digilogistist/The-Open-Source-USB-NES-Project/cap_add/IMG_20220502_140206 - Copy.jpg

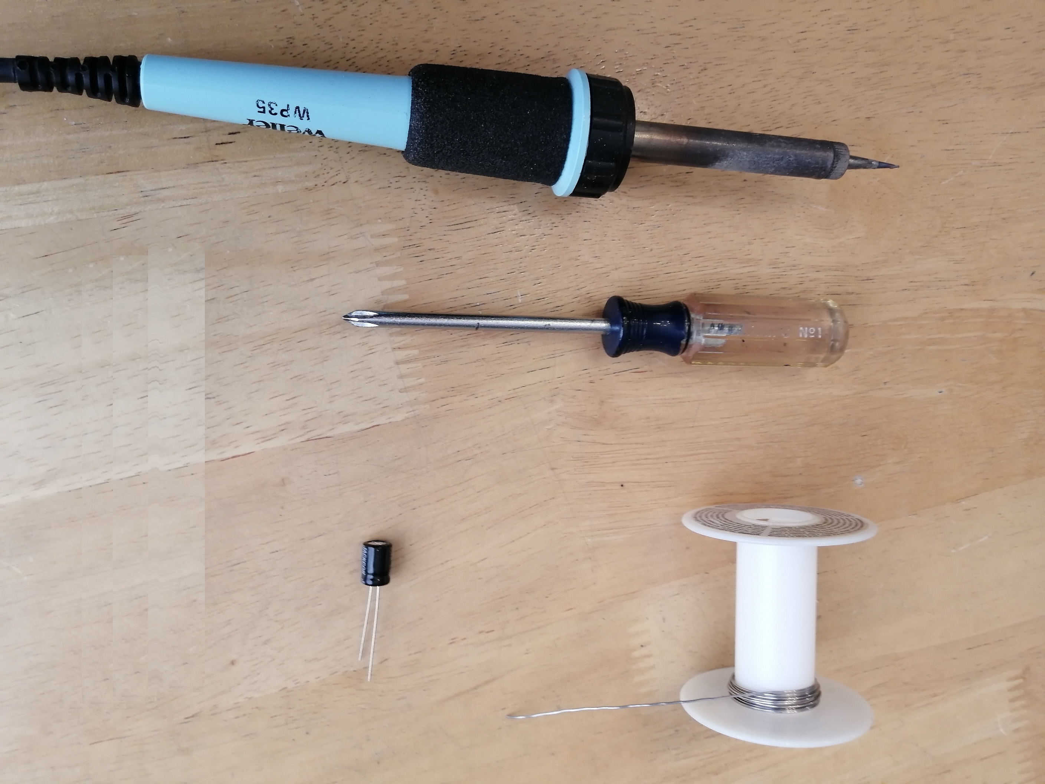
cap_add/IMG_20220502_140206 - Copy.jpg
