digilogistist/The-Open-Source-USB-NES-Project/cap_add/IMG_20220502_161517.jpg

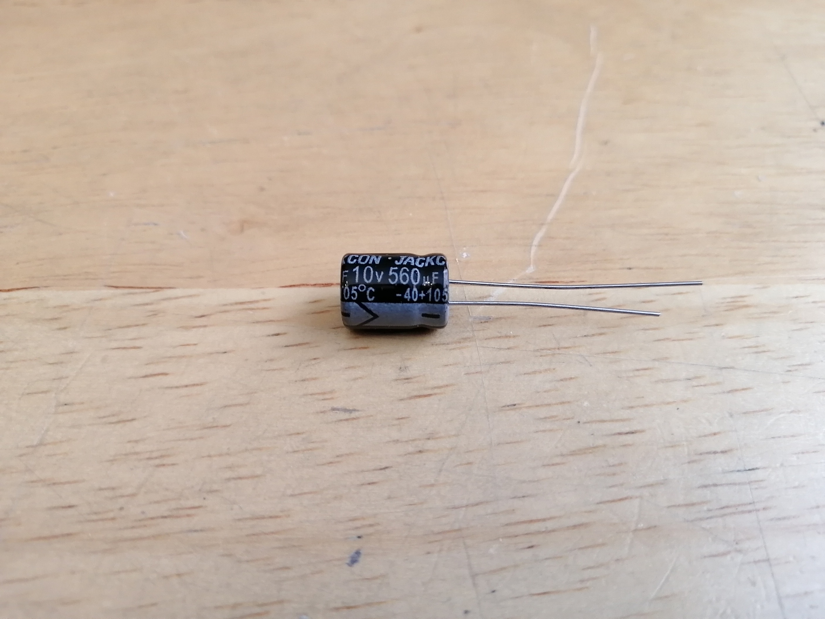
cap_add/IMG_20220502_161517.jpg
