digilogistist/The-Open-Source-USB-NES-Project/cap_add/IMG_20220503_070332.jpg

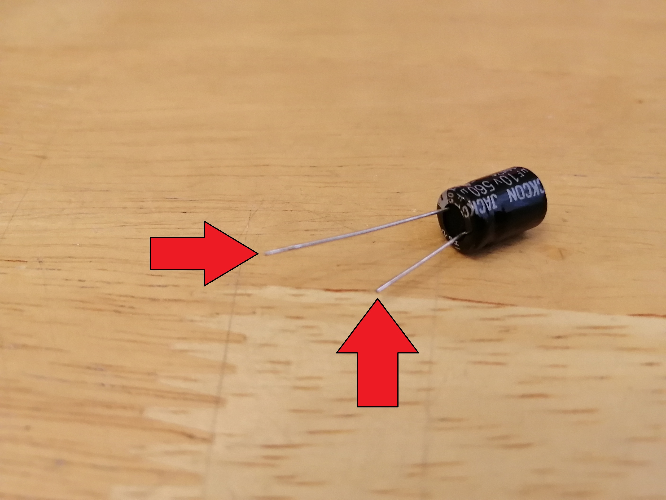
cap_add/IMG_20220503_070332.jpg
