digilogistist/The-Open-Source-USB-NES-Project/cap_add/IMG_20220503_071132.jpg

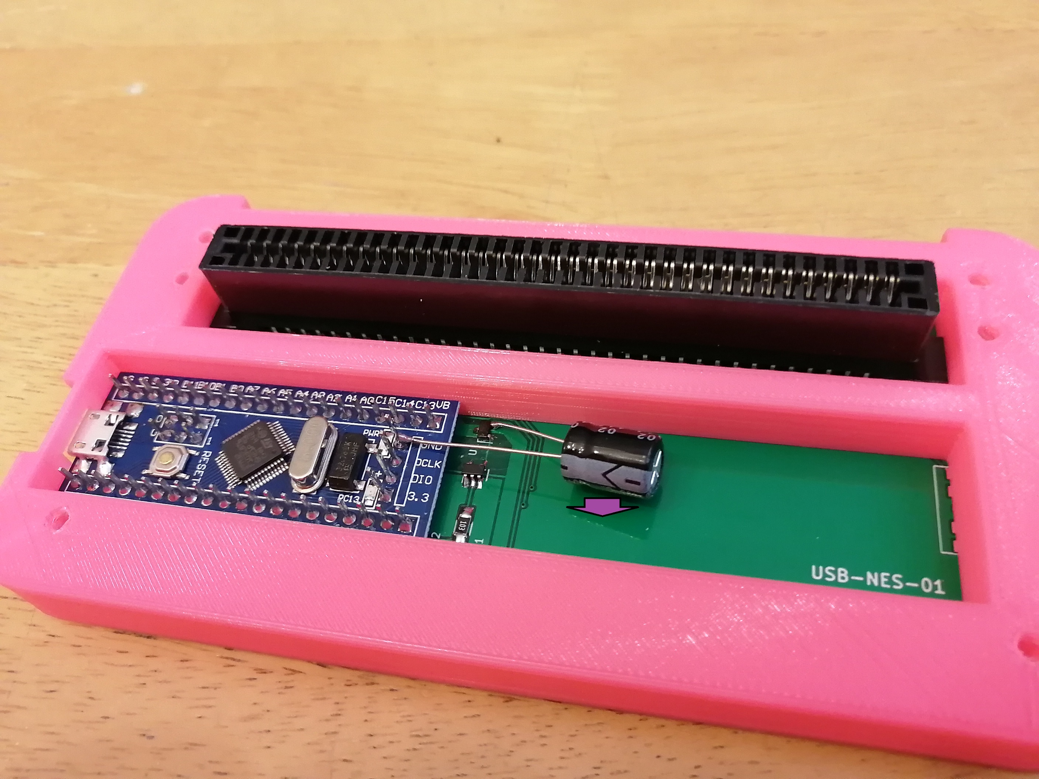
cap_add/IMG_20220503_071132.jpg
