digilogistist/The-Open-Source-USB-NES-Project/gallery/baby blue/IMG_20220524_081236.jpg

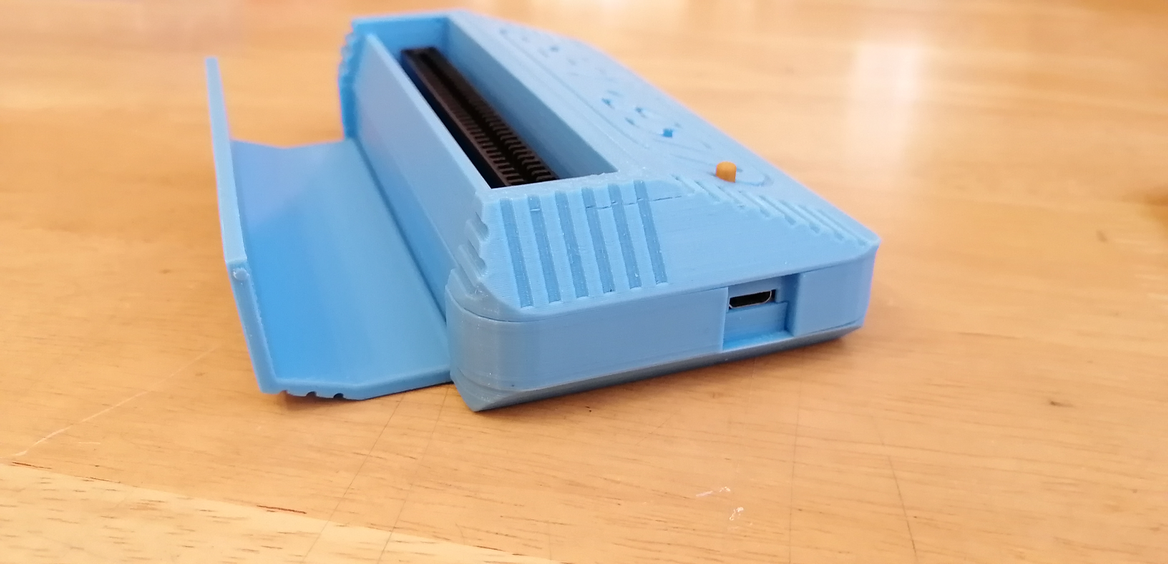
gallery/baby blue/IMG_20220524_081236.jpg
