digilogistist/The-Open-Source-USB-NES-Project/gallery/baby blue/IMG_20220524_081411.jpg

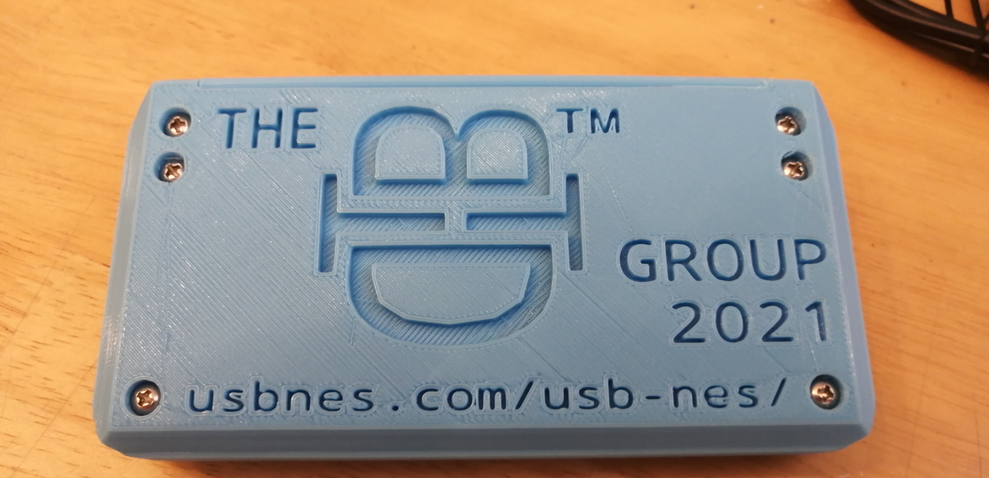
gallery/baby blue/IMG_20220524_081411.jpg
