digilogistist/The-Open-Source-USB-NES-Project/gallery/cartfail1.JPG

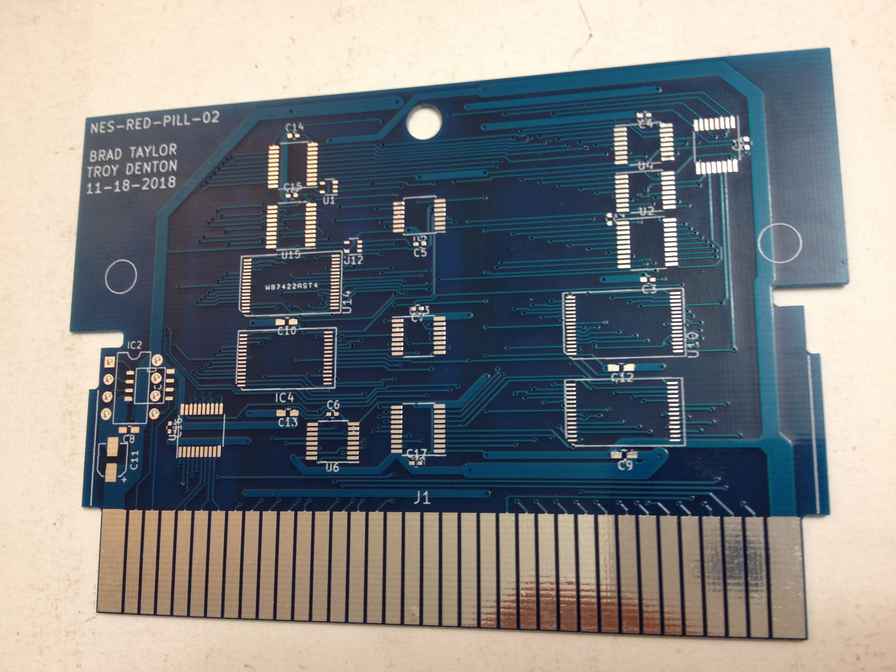
gallery/cartfail1.JPG
