digilogistist/The-Open-Source-USB-NES-Project/gallery/cartfail2.JPG

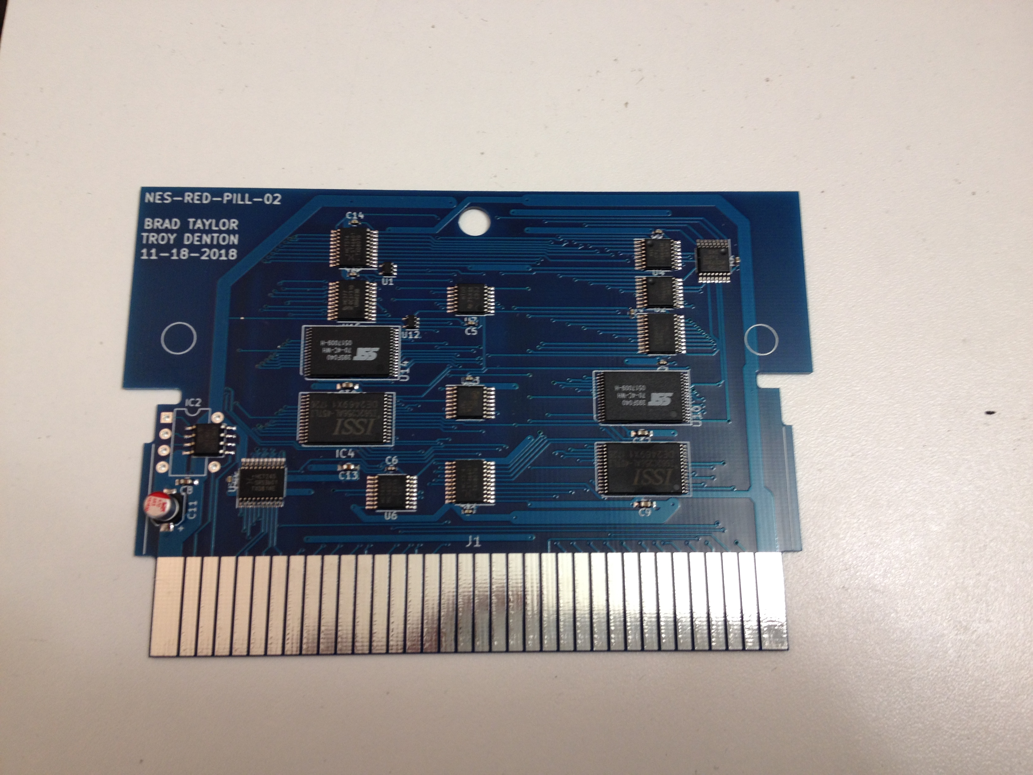
gallery/cartfail2.JPG
