digilogistist/The-Open-Source-USB-NES-Project/gallery/cartfail3.JPG

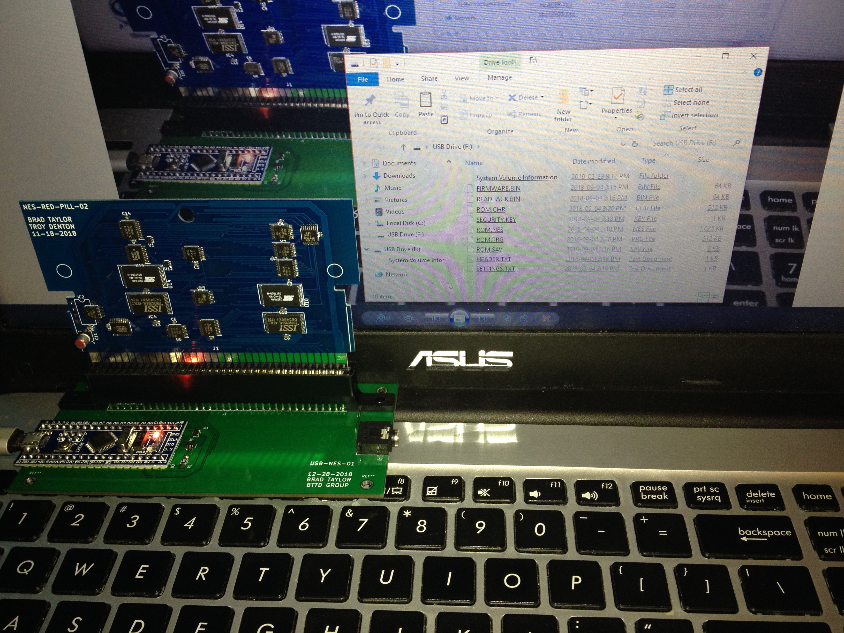
gallery/cartfail3.JPG
