digilogistist/The-Open-Source-USB-NES-Project/gallery/celluloid-shot0002.jpg

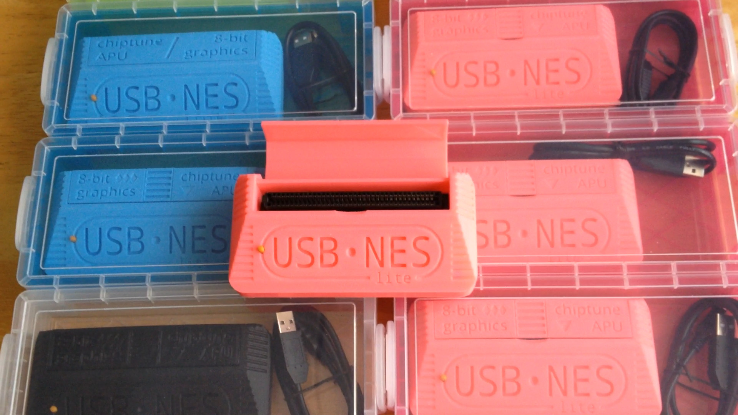
gallery/celluloid-shot0002.jpg
