digilogistist/The-Open-Source-USB-NES-Project/gallery/DIY kit/IMG_1746.JPG

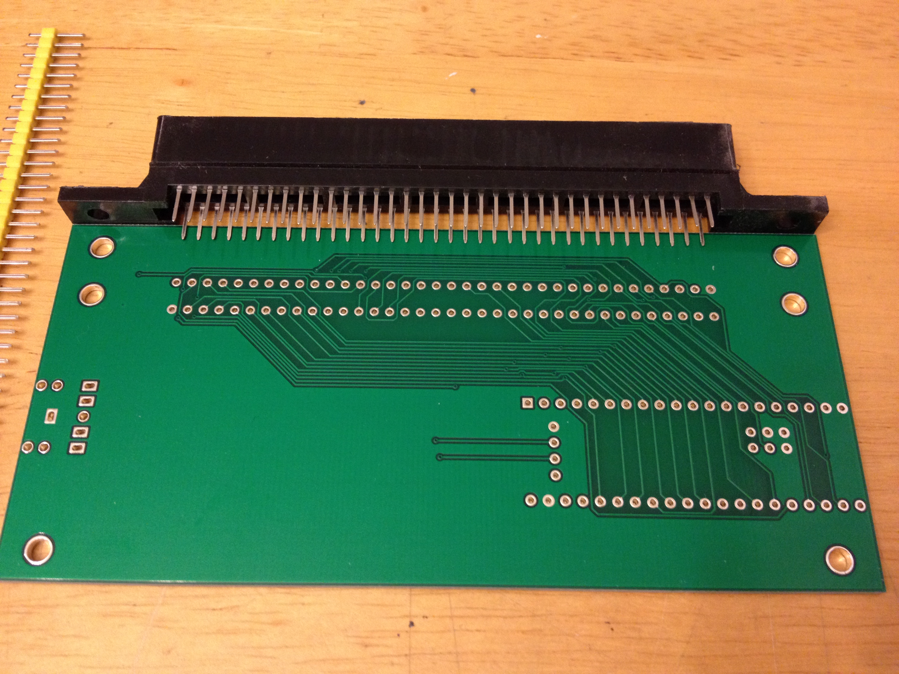
gallery/DIY kit/IMG_1746.JPG
