digilogistist/The-Open-Source-USB-NES-Project/gallery/DIY kit/IMG_1748.JPG

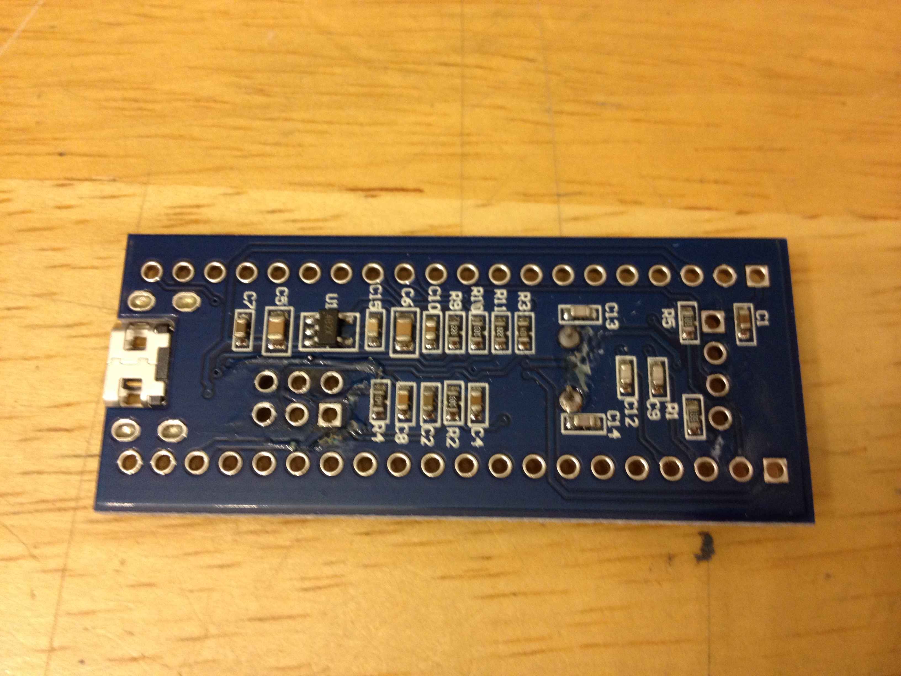
gallery/DIY kit/IMG_1748.JPG
