digilogistist/The-Open-Source-USB-NES-Project/gallery/DIY kit/IMG_1896.JPG

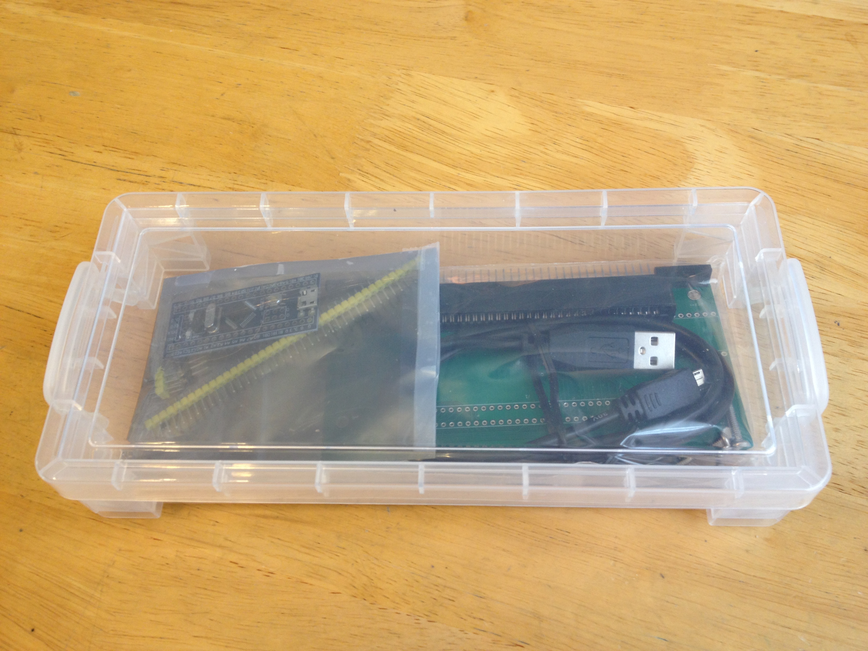
gallery/DIY kit/IMG_1896.JPG
