digilogistist/The-Open-Source-USB-NES-Project/gallery/DIY kit/IMG_1899.JPG

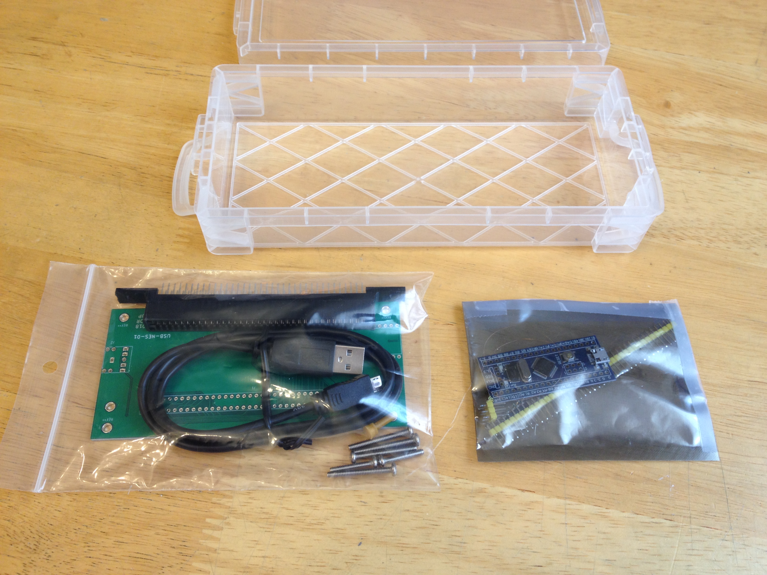
gallery/DIY kit/IMG_1899.JPG
