digilogistist/The-Open-Source-USB-NES-Project/gallery/fluorescent yellow/IMG_1937.JPG

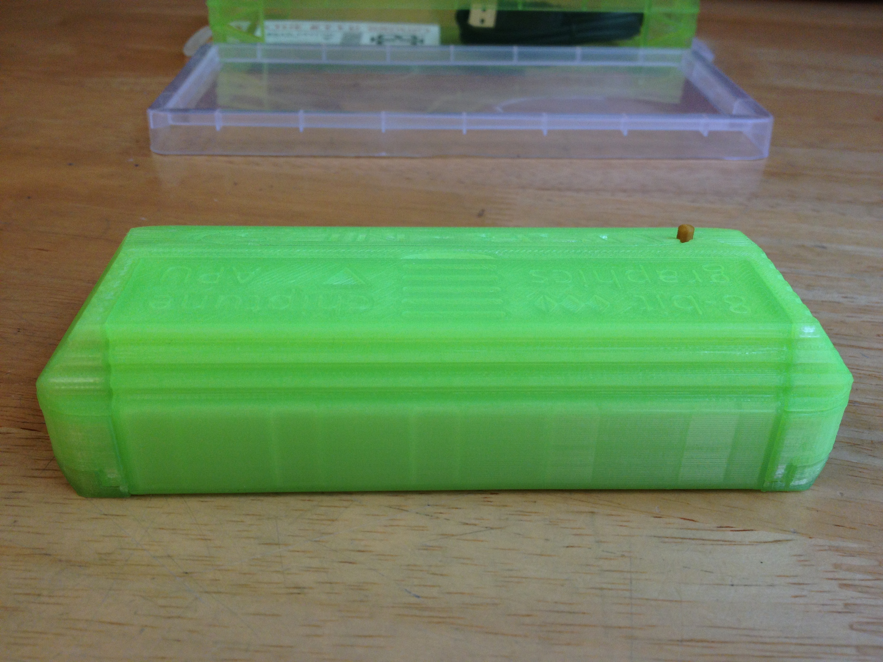
gallery/fluorescent yellow/IMG_1937.JPG
