digilogistist/The-Open-Source-USB-NES-Project/gallery/fluorescent yellow/IMG_1939.JPG

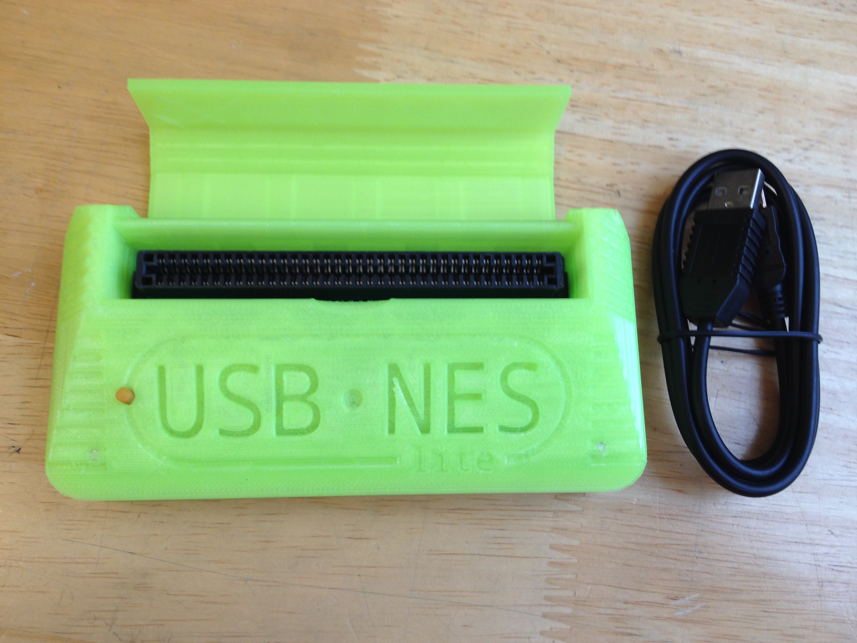
gallery/fluorescent yellow/IMG_1939.JPG
