digilogistist/The-Open-Source-USB-NES-Project/gallery/fluorescent yellow/IMG_1953.JPG

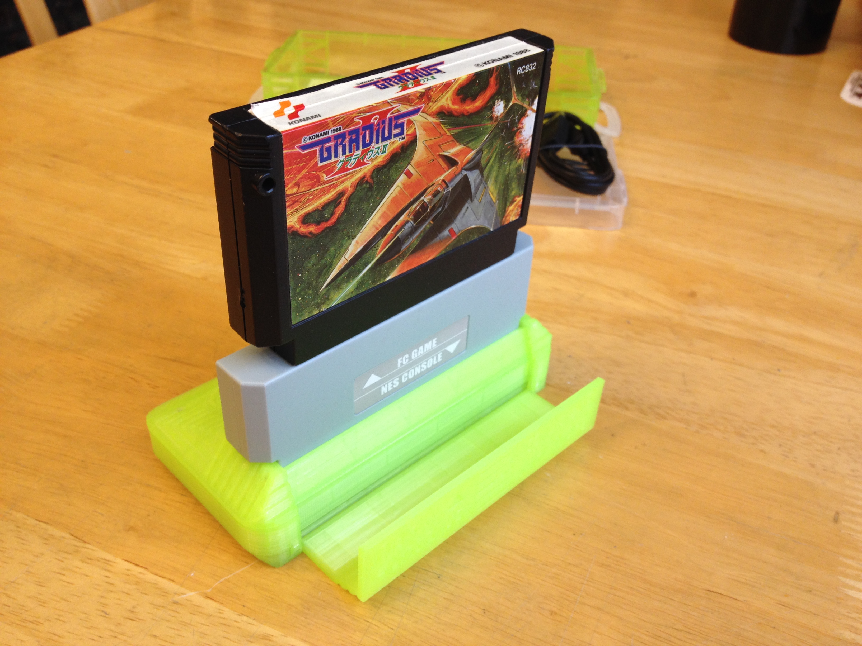
gallery/fluorescent yellow/IMG_1953.JPG
