digilogistist/The-Open-Source-USB-NES-Project/gallery/glittery gold/IMG_20230323_132124.jpg

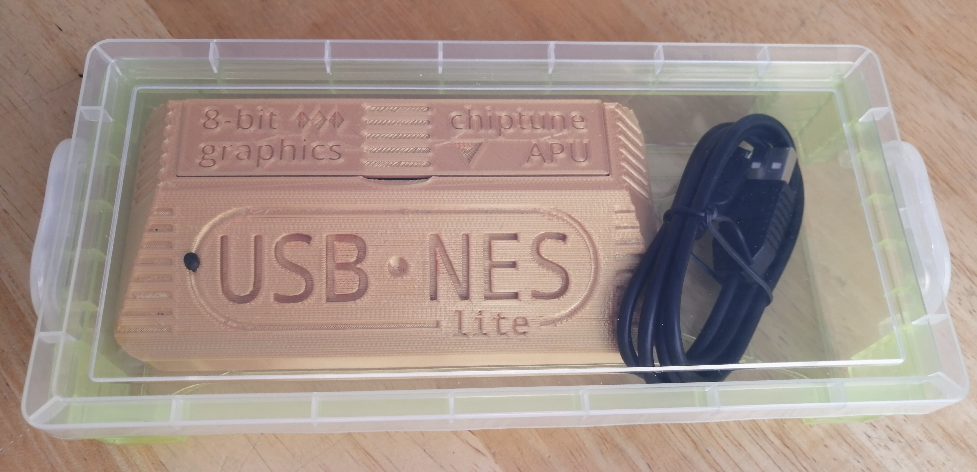
gallery/glittery gold/IMG_20230323_132124.jpg
