digilogistist/The-Open-Source-USB-NES-Project/gallery/glittery gold/IMG_20230323_132413.jpg

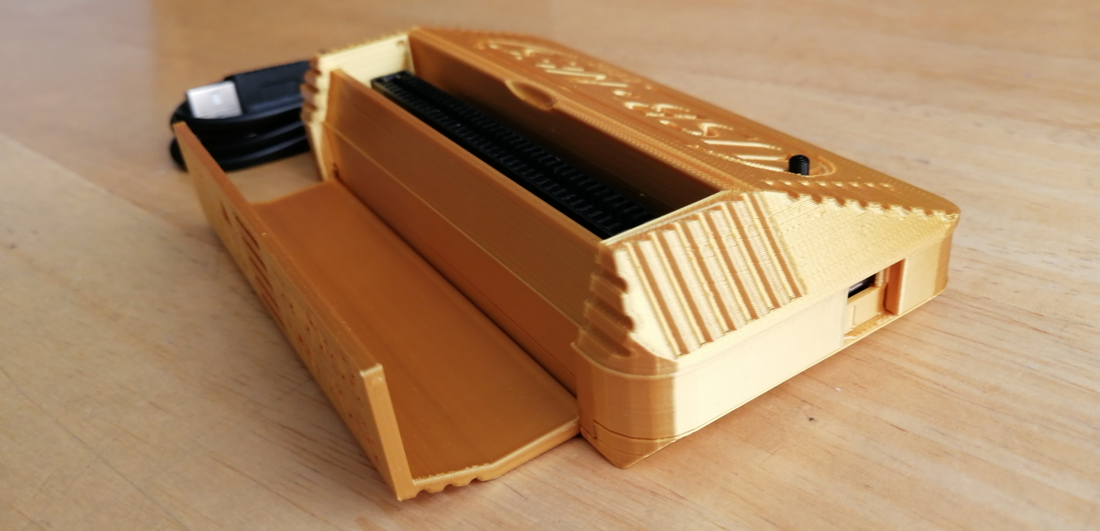
gallery/glittery gold/IMG_20230323_132413.jpg
