digilogistist/The-Open-Source-USB-NES-Project/gallery/gummy green/IMG_1789.JPG

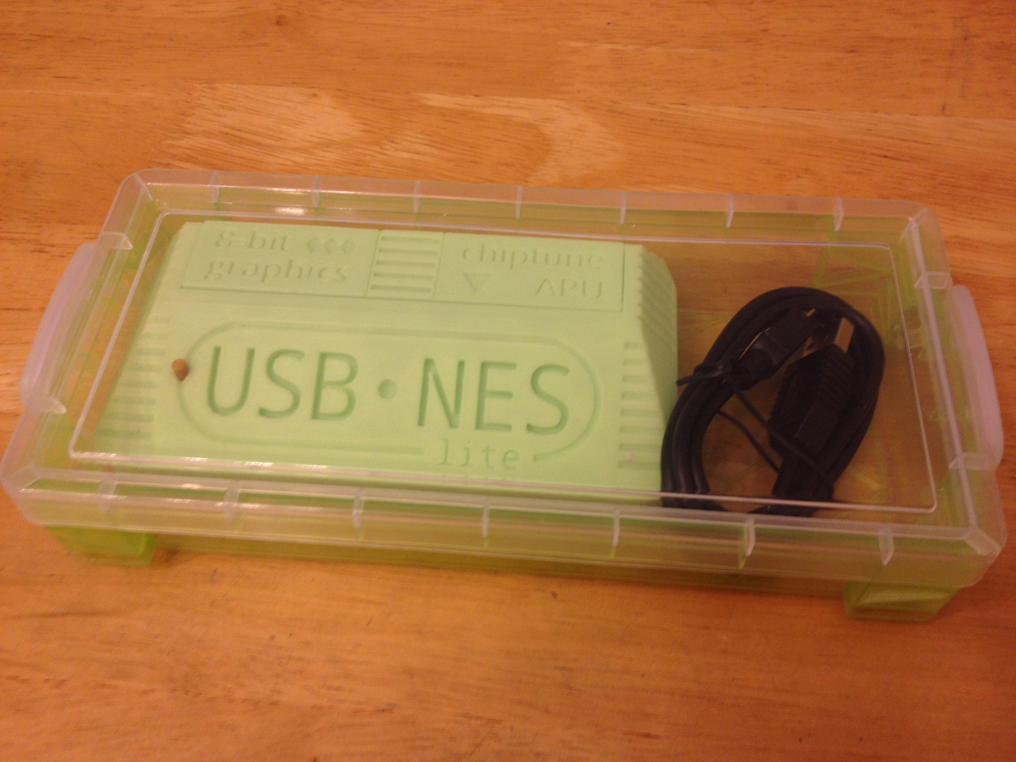
gallery/gummy green/IMG_1789.JPG
