digilogistist/The-Open-Source-USB-NES-Project/gallery/gummy green/IMG_1792.JPG

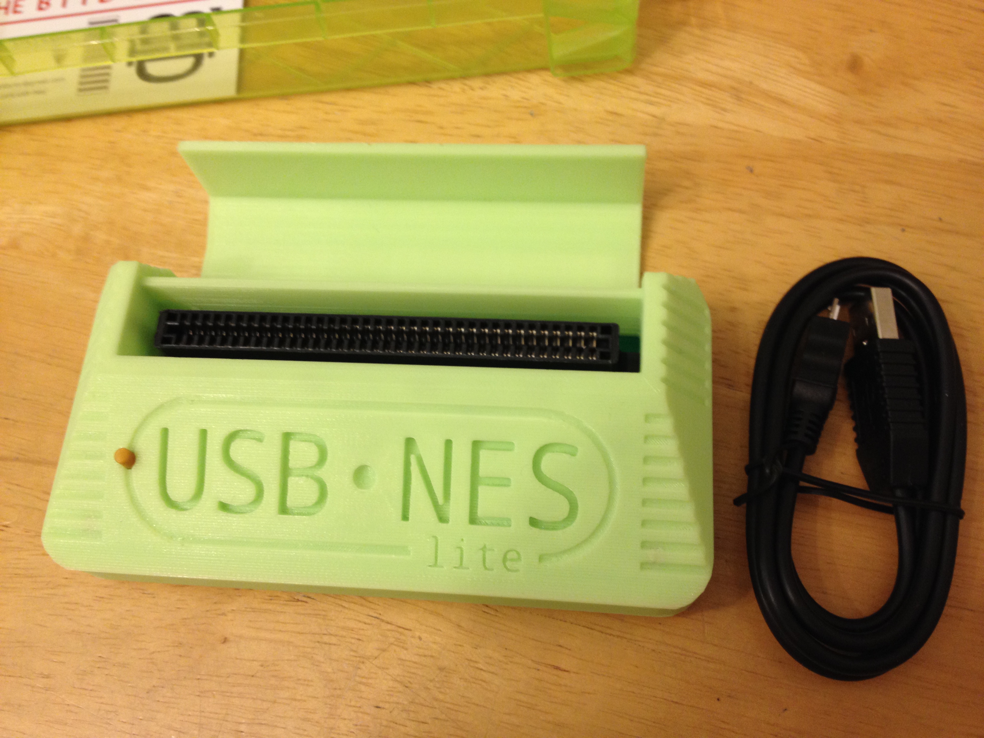
gallery/gummy green/IMG_1792.JPG
