digilogistist/The-Open-Source-USB-NES-Project/gallery/gummy green/IMG_1841.JPG

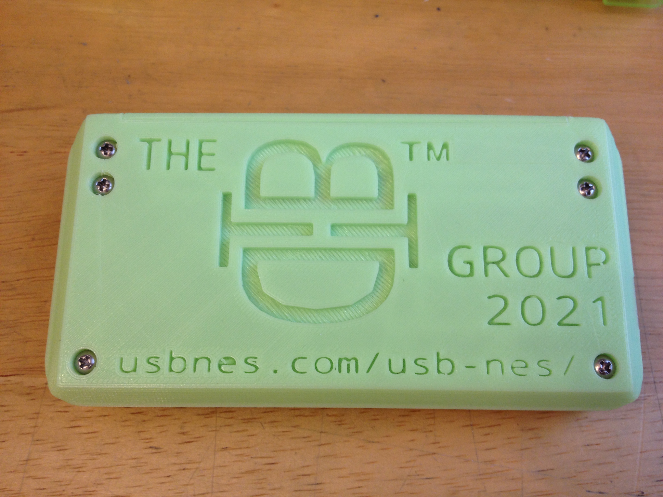
gallery/gummy green/IMG_1841.JPG
