digilogistist/The-Open-Source-USB-NES-Project/gallery/gummy green/IMG_1852.JPG

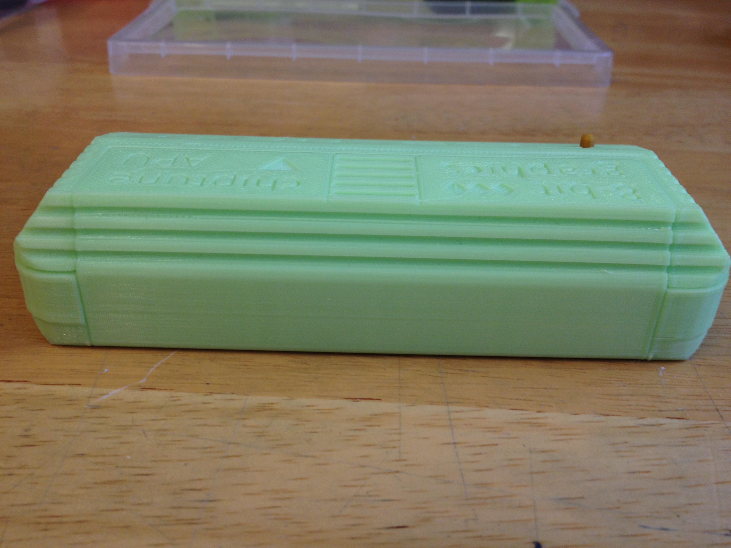
gallery/gummy green/IMG_1852.JPG
