digilogistist/The-Open-Source-USB-NES-Project/gallery/IMG_1150.JPG

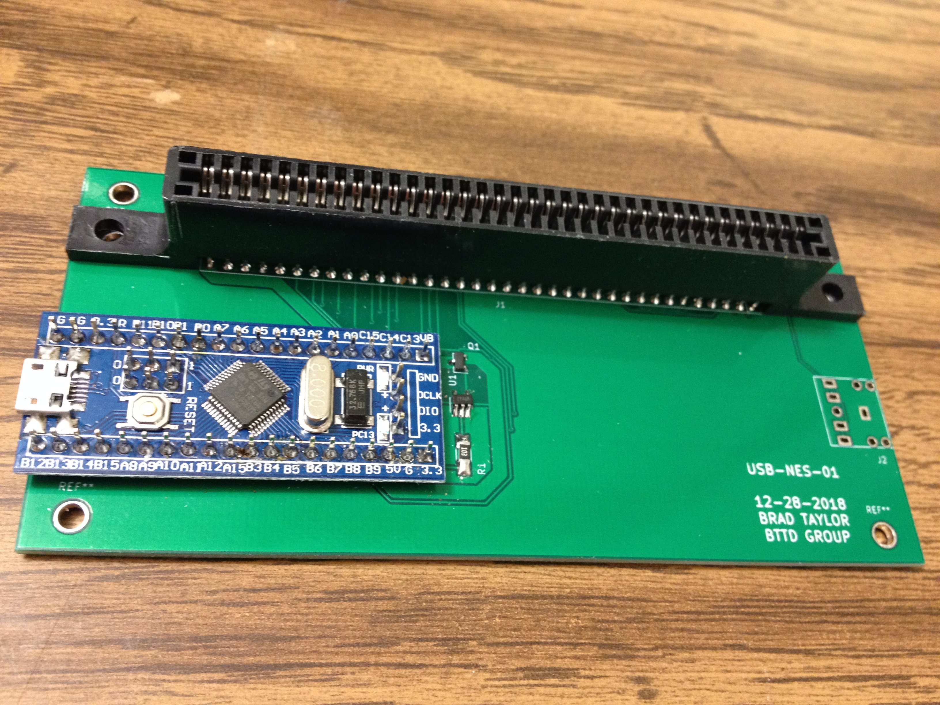
gallery/IMG_1150.JPG
