digilogistist/The-Open-Source-USB-NES-Project/gallery/IMG_1157.JPG

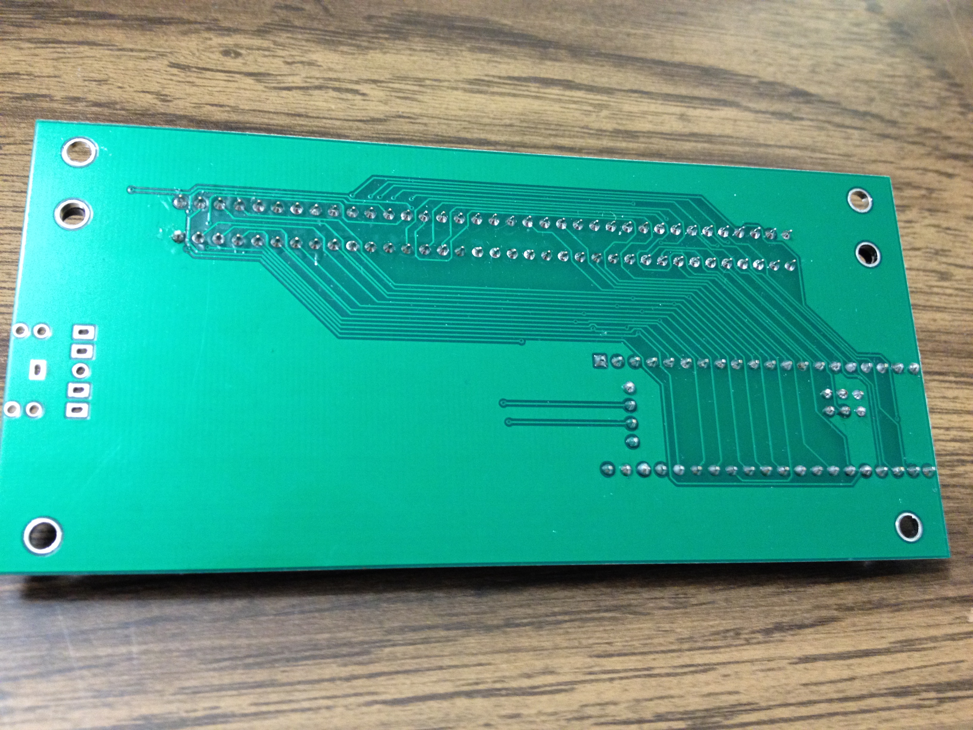
gallery/IMG_1157.JPG
