digilogistist/The-Open-Source-USB-NES-Project/gallery/IMG_1705.JPG

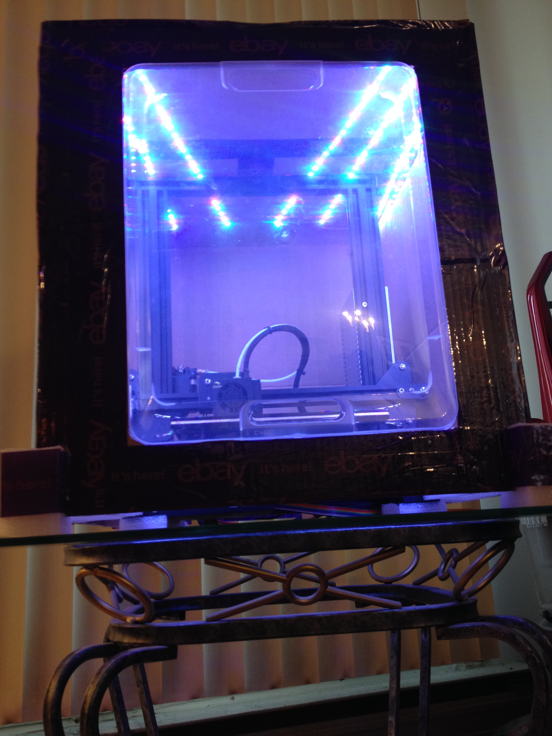
gallery/IMG_1705.JPG
