digilogistist/The-Open-Source-USB-NES-Project/gallery/IMG_1709.JPG

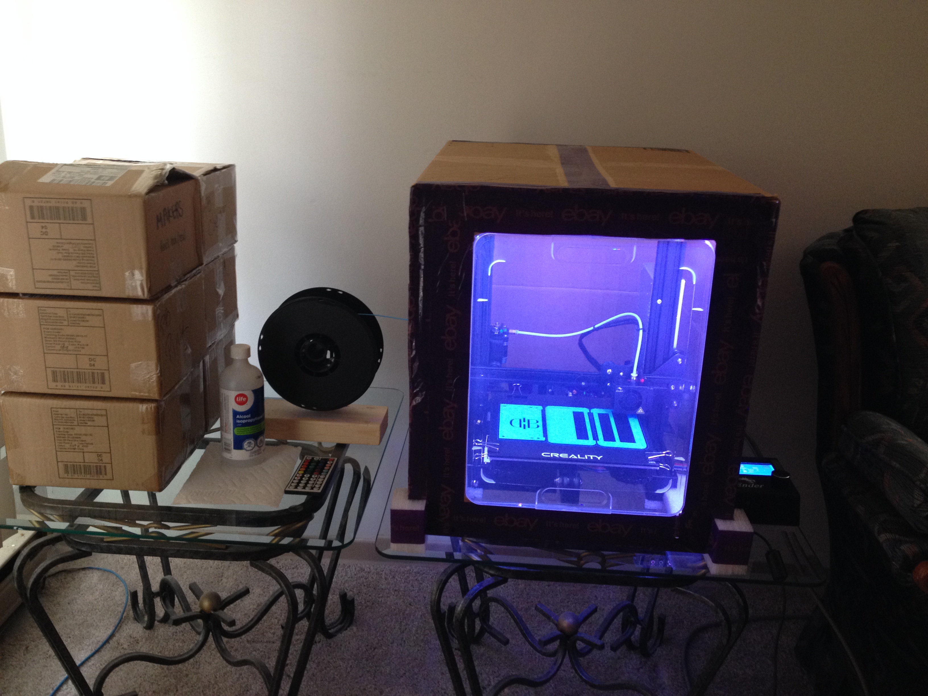
gallery/IMG_1709.JPG
