digilogistist/The-Open-Source-USB-NES-Project/gallery/IMG_1710.JPG

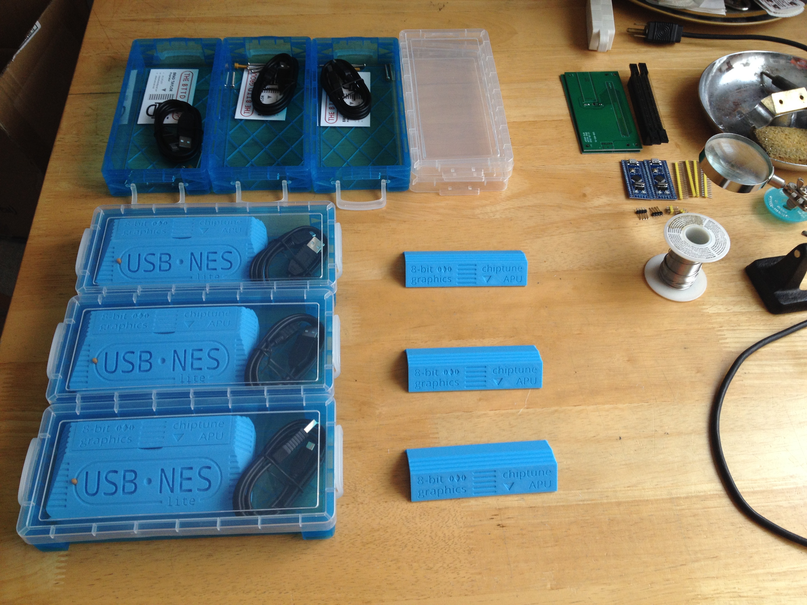
gallery/IMG_1710.JPG
