digilogistist/The-Open-Source-USB-NES-Project/gallery/IMG_1750.JPG

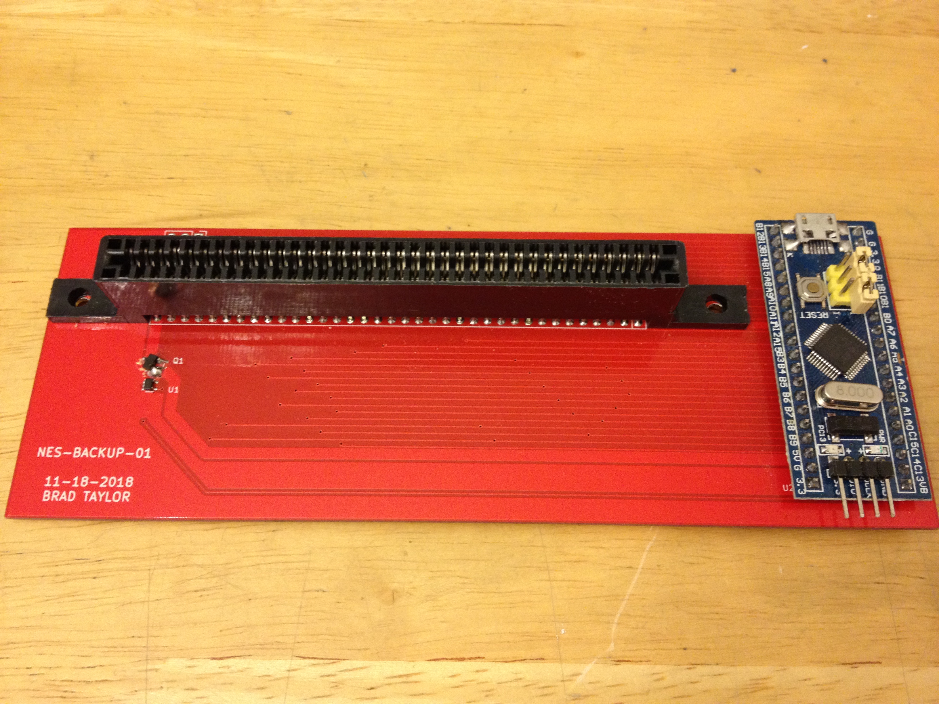
gallery/IMG_1750.JPG
