digilogistist/The-Open-Source-USB-NES-Project/gallery/IMG_1752.JPG

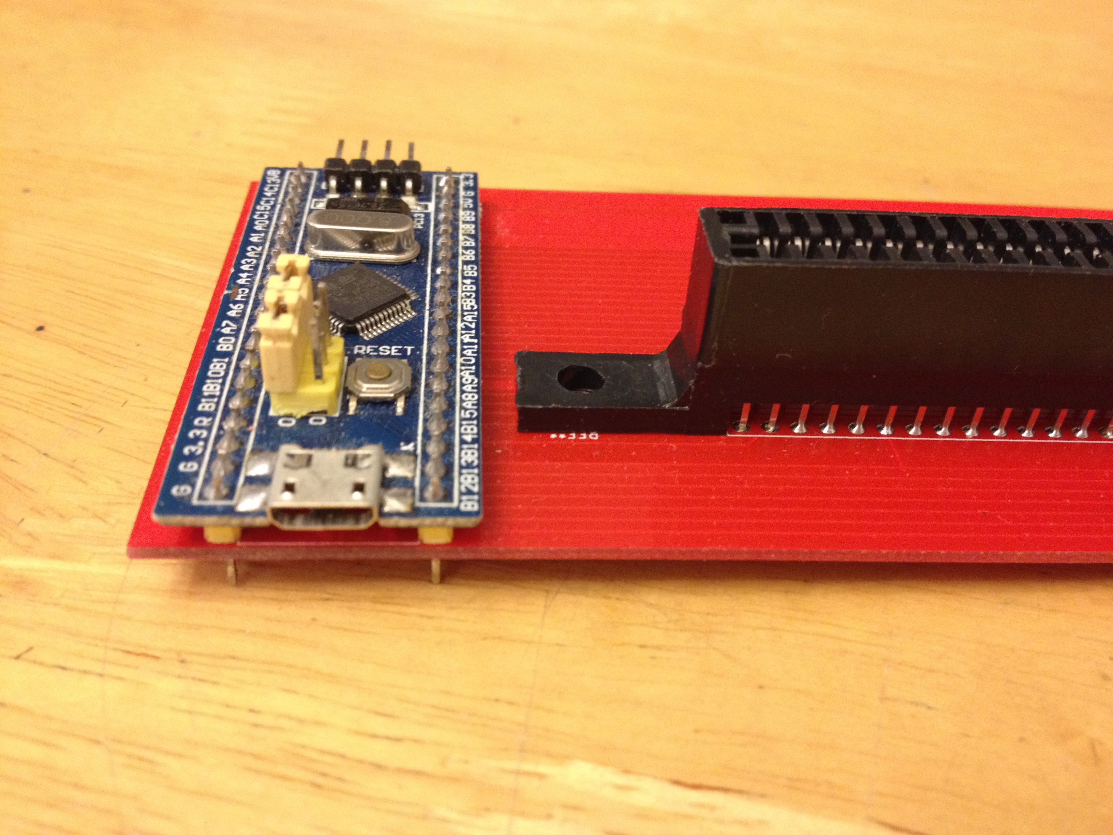
gallery/IMG_1752.JPG
