digilogistist/The-Open-Source-USB-NES-Project/gallery/IMG_1754.JPG

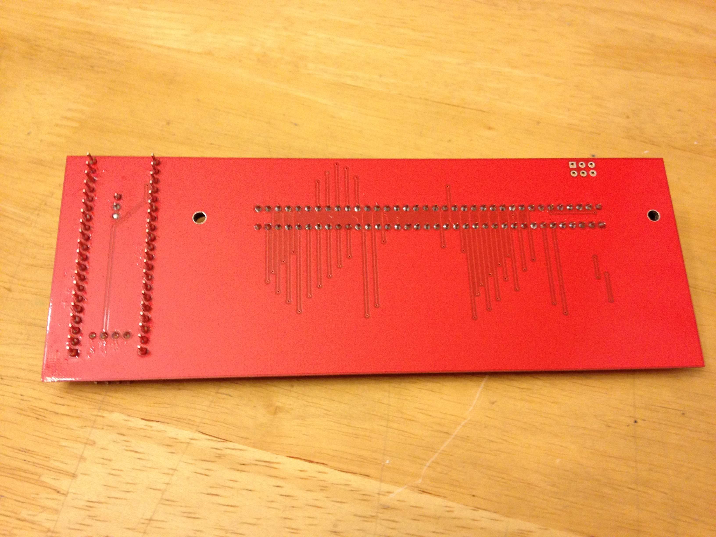
gallery/IMG_1754.JPG
