digilogistist/The-Open-Source-USB-NES-Project/gallery/IMG_1831.JPG

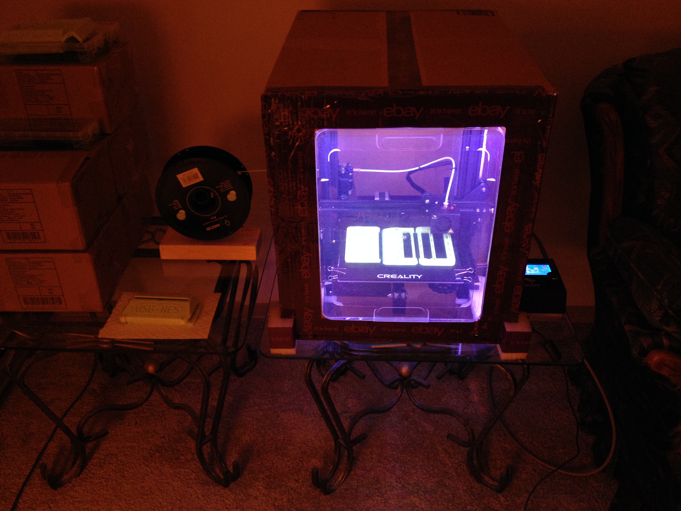
gallery/IMG_1831.JPG
