digilogistist/The-Open-Source-USB-NES-Project/gallery/IMG_1833.JPG

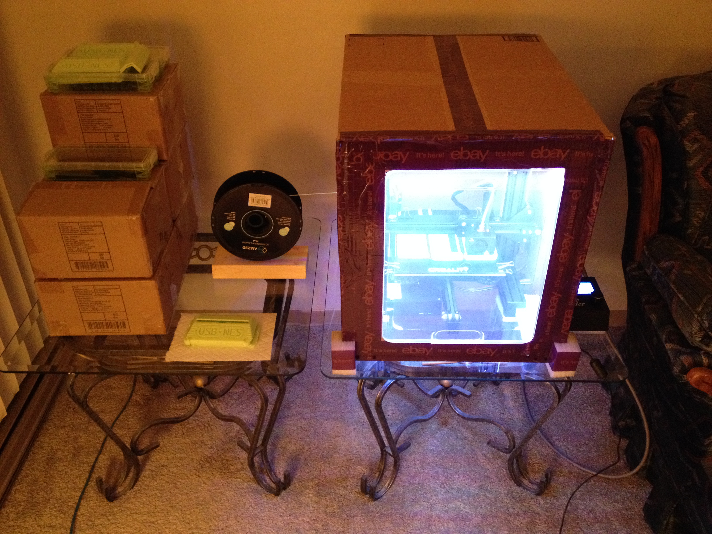
gallery/IMG_1833.JPG
