digilogistist/The-Open-Source-USB-NES-Project/gallery/IMG_1835.JPG

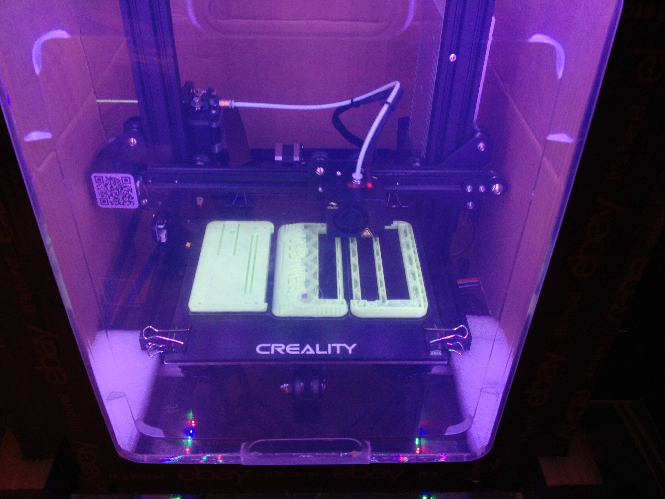
gallery/IMG_1835.JPG
