digilogistist/The-Open-Source-USB-NES-Project/gallery/IMG_20230210_214148.jpg

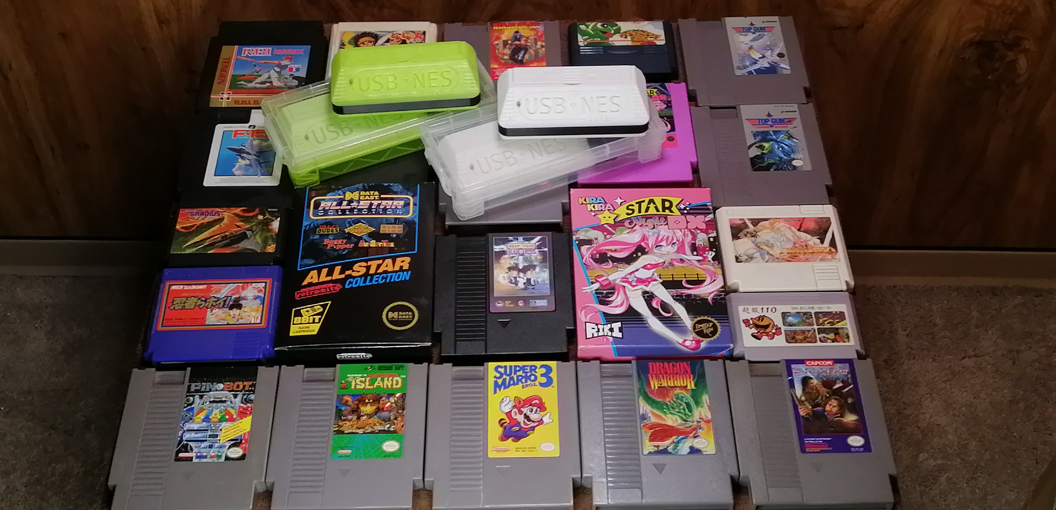
gallery/IMG_20230210_214148.jpg
