digilogistist/The-Open-Source-USB-NES-Project/gallery/NES-BACKUP (proto).JPG

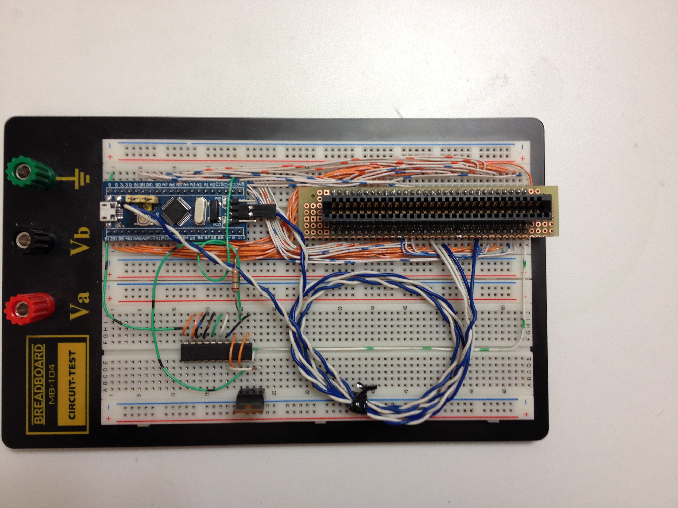
gallery/NES-BACKUP (proto).JPG
