digilogistist/The-Open-Source-USB-NES-Project/gallery/NES-BACKUP back (unpop).JPG

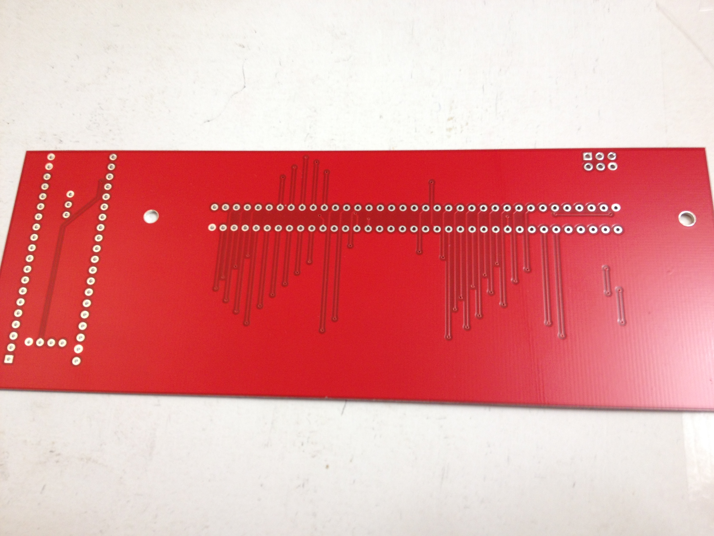
gallery/NES-BACKUP back (unpop).JPG
