digilogistist/The-Open-Source-USB-NES-Project/gallery/NES-BACKUP running.JPG

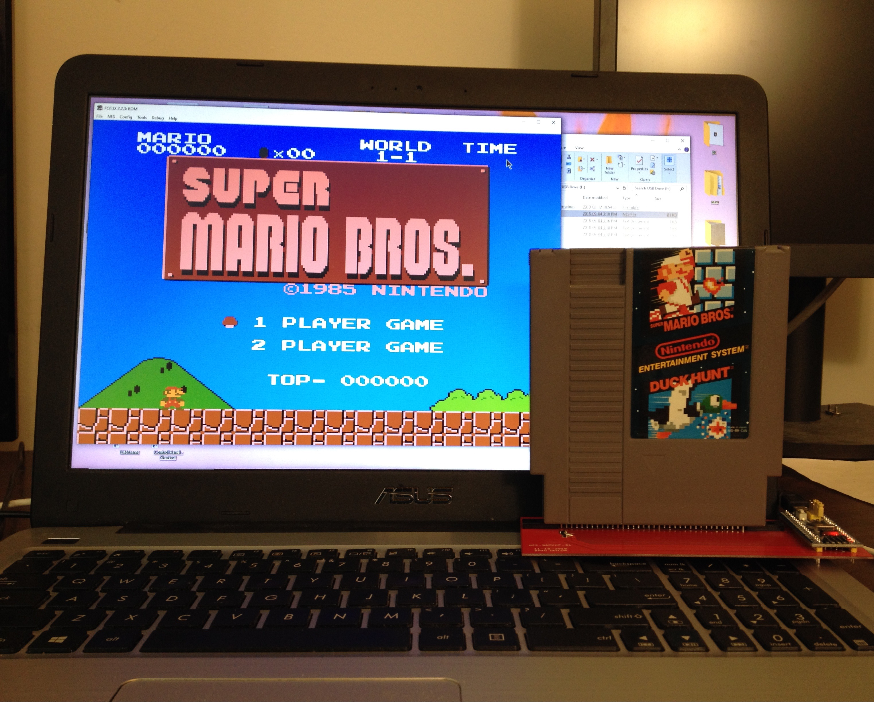
gallery/NES-BACKUP running.JPG
