digilogistist/The-Open-Source-USB-NES-Project/gallery/PCB WAY.JPG

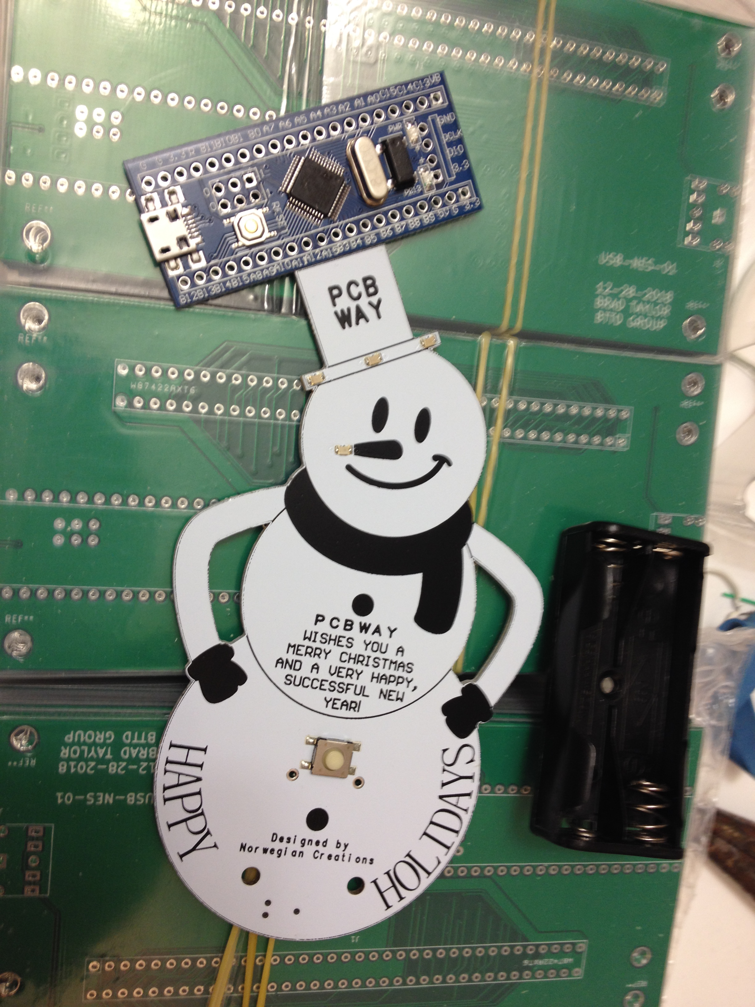
gallery/PCB WAY.JPG
