digilogistist/The-Open-Source-USB-NES-Project/gallery/phat black/IMG_1755.JPG

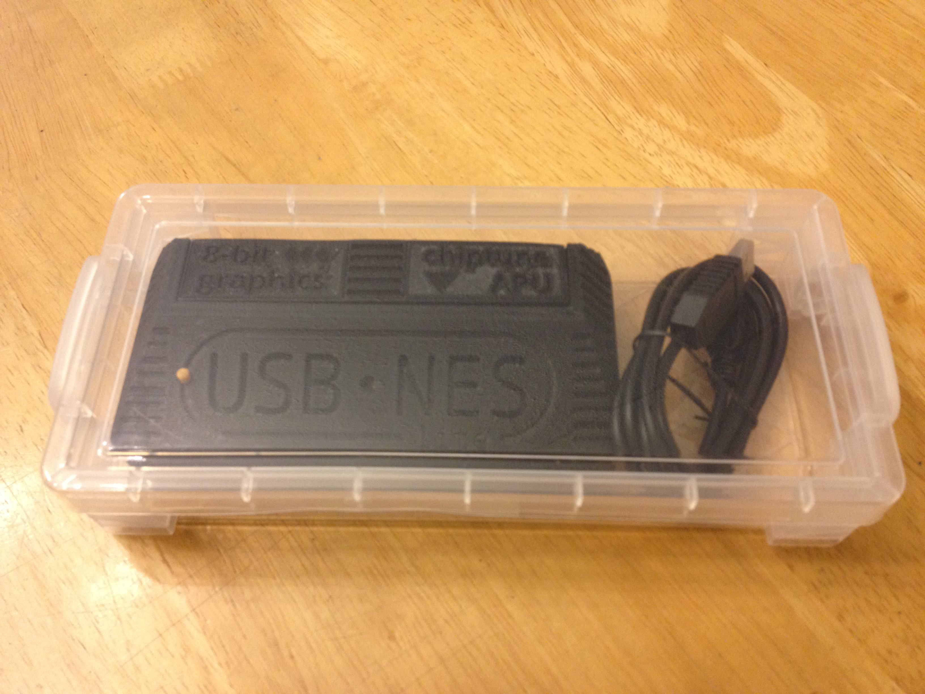
gallery/phat black/IMG_1755.JPG
