digilogistist/The-Open-Source-USB-NES-Project/gallery/phat black/IMG_1759.JPG

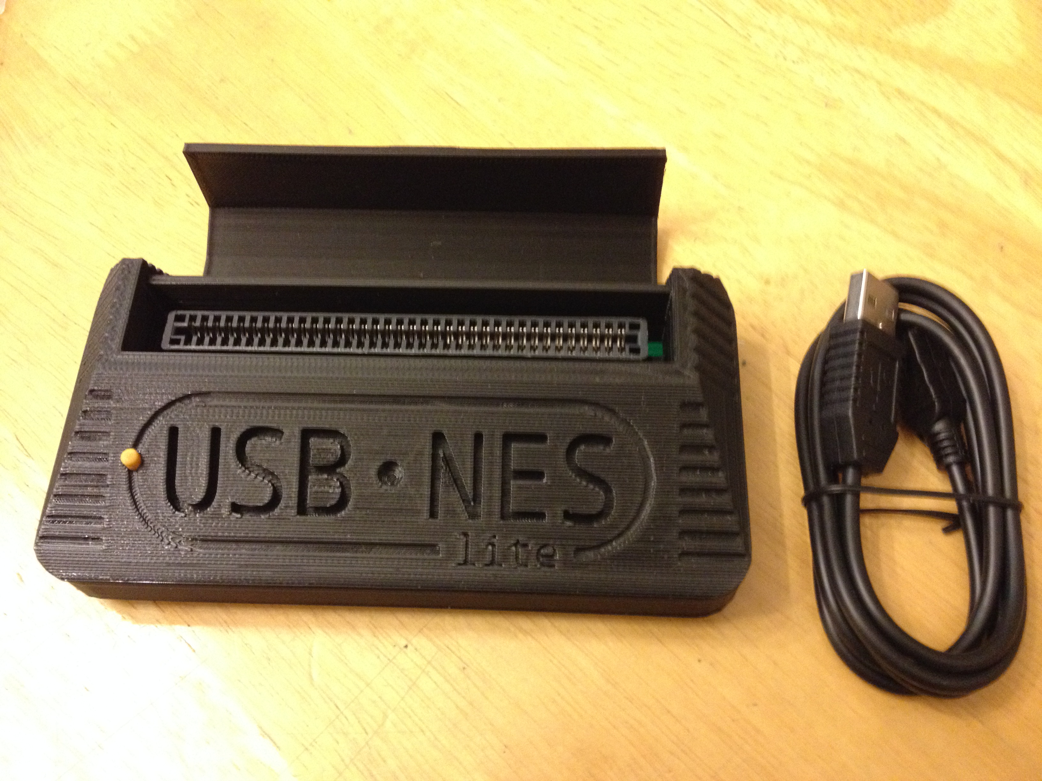
gallery/phat black/IMG_1759.JPG
