digilogistist/The-Open-Source-USB-NES-Project/gallery/phat black/IMG_1763.JPG

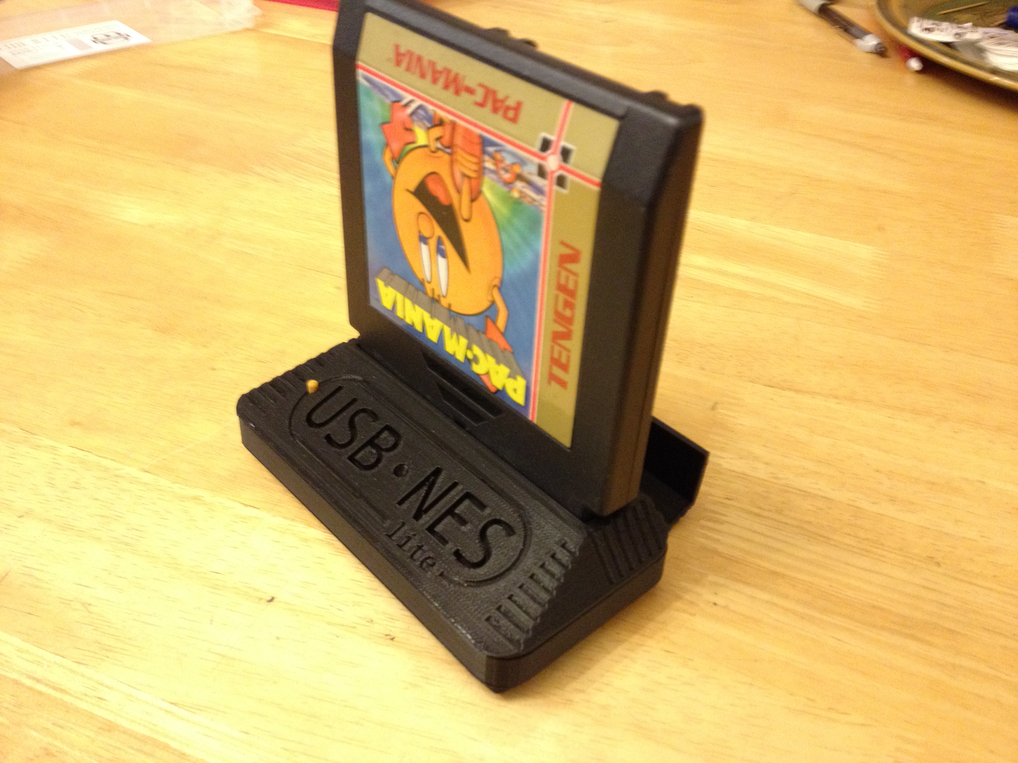
gallery/phat black/IMG_1763.JPG
