digilogistist/The-Open-Source-USB-NES-Project/gallery/phat black/IMG_1883.JPG

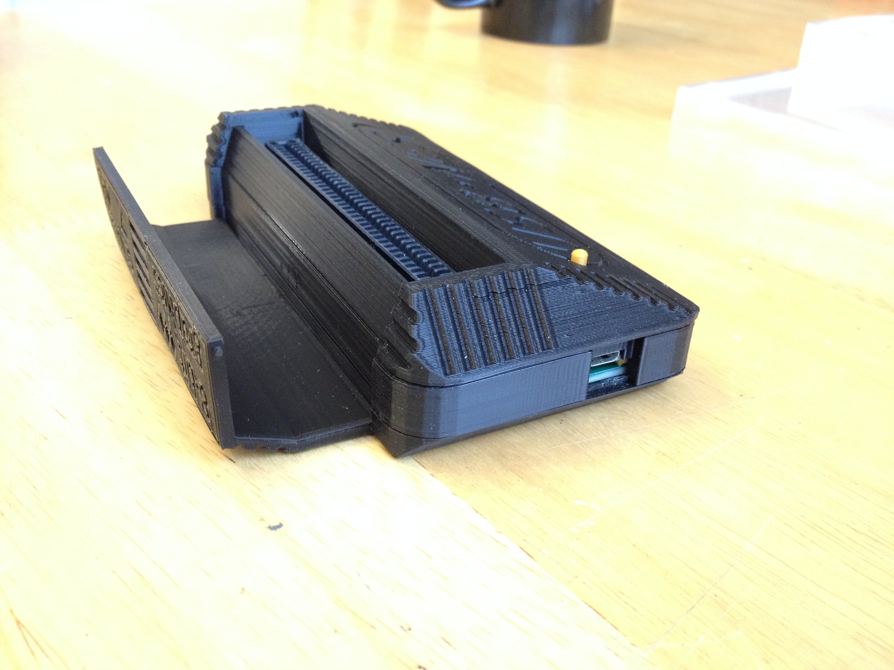
gallery/phat black/IMG_1883.JPG
