digilogistist/The-Open-Source-USB-NES-Project/gallery/pretty pink/IMG_20220524_082223.jpg

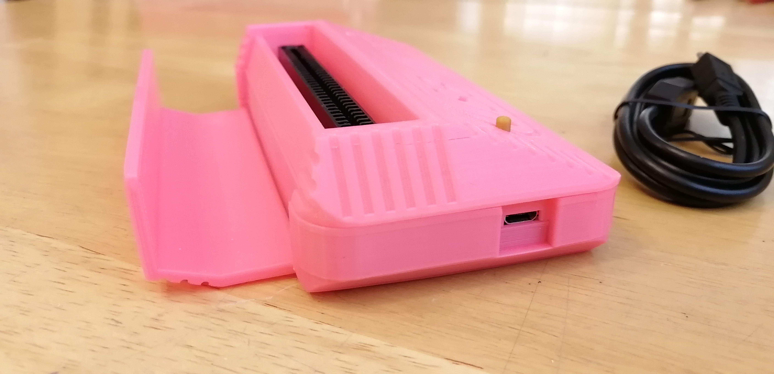
gallery/pretty pink/IMG_20220524_082223.jpg
