digilogistist/The-Open-Source-USB-NES-Project/gallery/pretty pink/IMG_20220524_082250.jpg

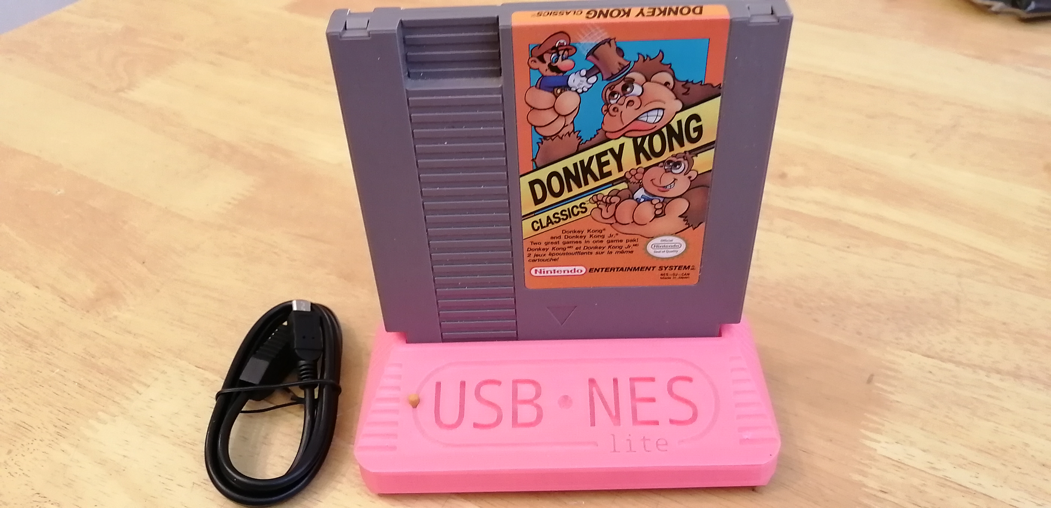
gallery/pretty pink/IMG_20220524_082250.jpg
