digilogistist/The-Open-Source-USB-NES-Project/gallery/pretty pink/IMG_20220524_082401.jpg

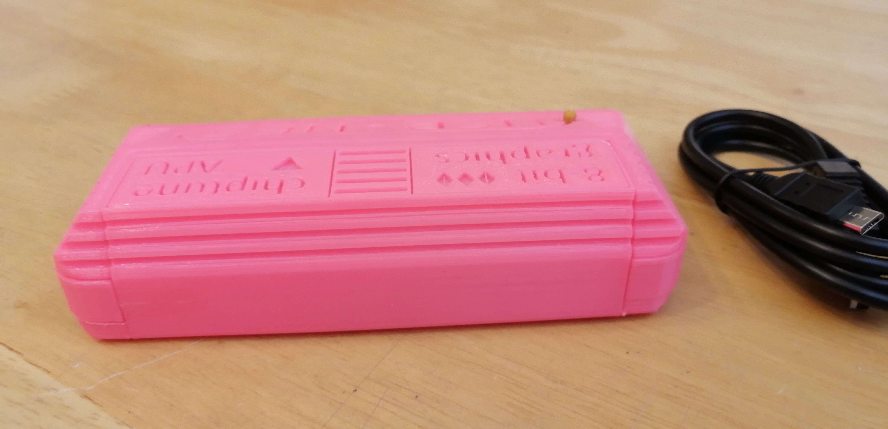
gallery/pretty pink/IMG_20220524_082401.jpg
