digilogistist/The-Open-Source-USB-NES-Project/gallery/Screenshot_2023-04-13_22-23-41.png

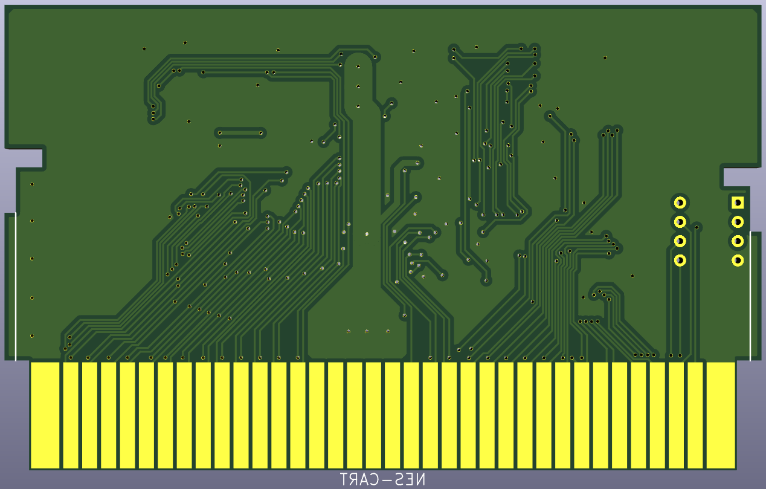
gallery/Screenshot_2023-04-13_22-23-41.png
