digilogistist/The-Open-Source-USB-NES-Project/gallery/Screenshot_2023-04-13_22-25-45.png

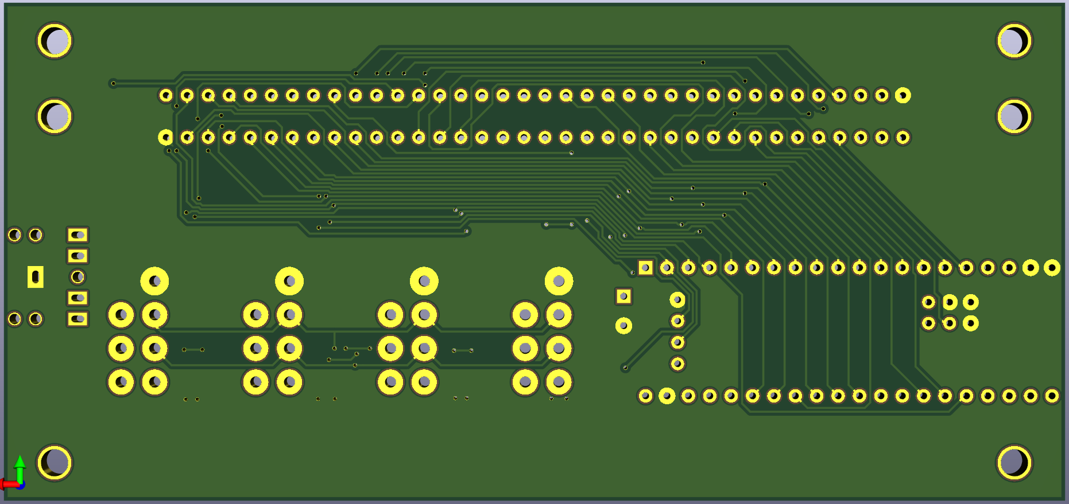
gallery/Screenshot_2023-04-13_22-25-45.png
