digilogistist/The-Open-Source-USB-NES-Project/gallery/shiny silver/IMG_20230317_122905.jpg

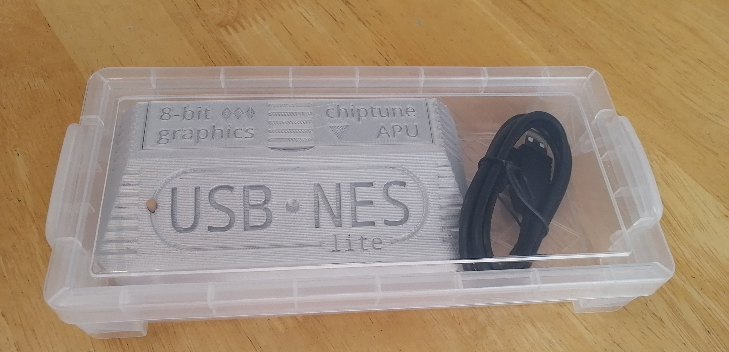
gallery/shiny silver/IMG_20230317_122905.jpg
