digilogistist/The-Open-Source-USB-NES-Project/gallery/shiny silver/IMG_20230317_123012.jpg

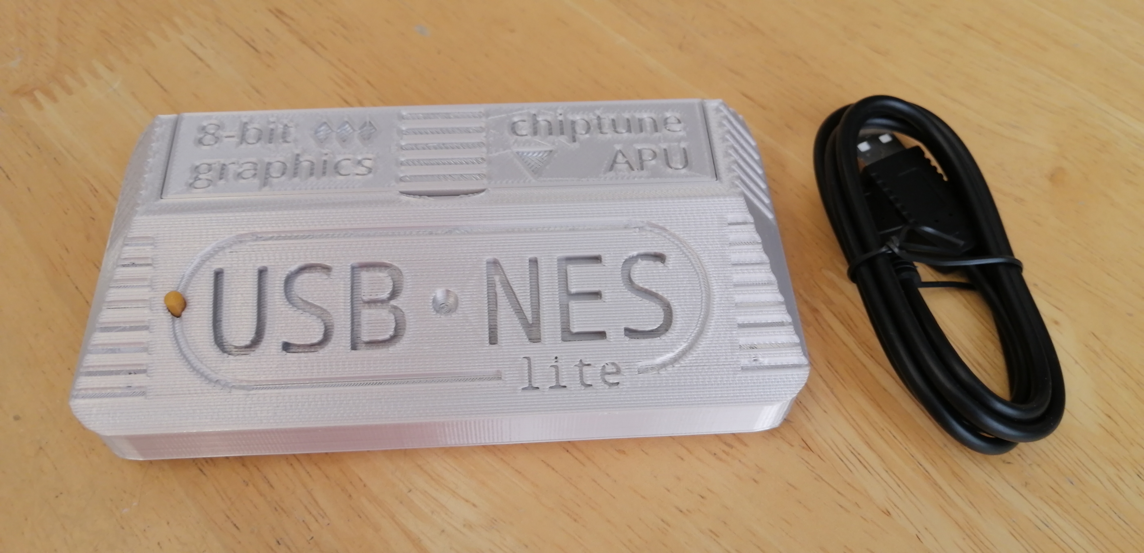
gallery/shiny silver/IMG_20230317_123012.jpg
