digilogistist/The-Open-Source-USB-NES-Project/gallery/shiny silver/IMG_20230317_123150.jpg

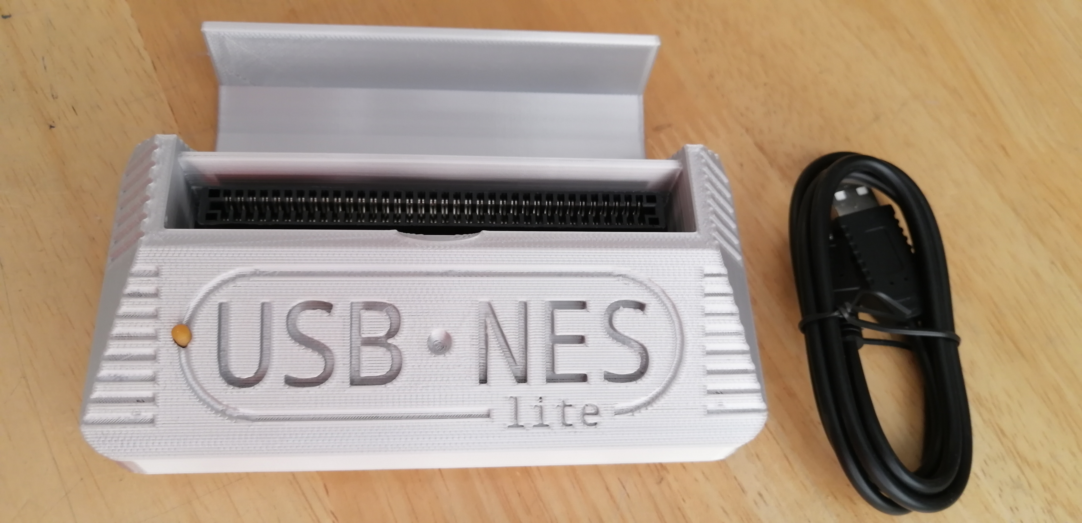
gallery/shiny silver/IMG_20230317_123150.jpg
