digilogistist/The-Open-Source-USB-NES-Project/gallery/USB-NES back (unpop).JPG

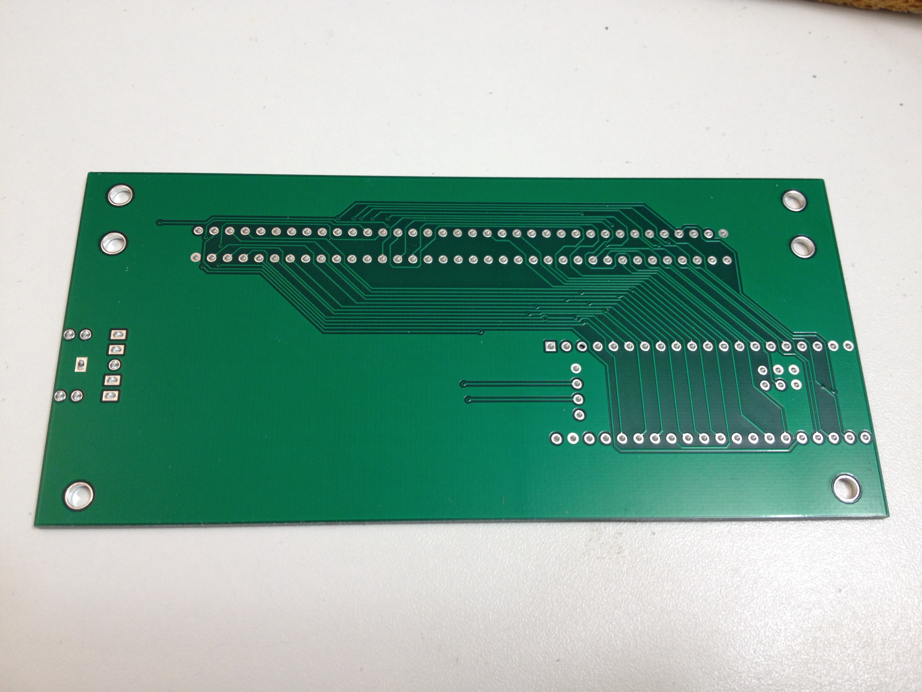
gallery/USB-NES back (unpop).JPG
