digilogistist/The-Open-Source-USB-NES-Project/gallery/USB-NES front (unpop).JPG

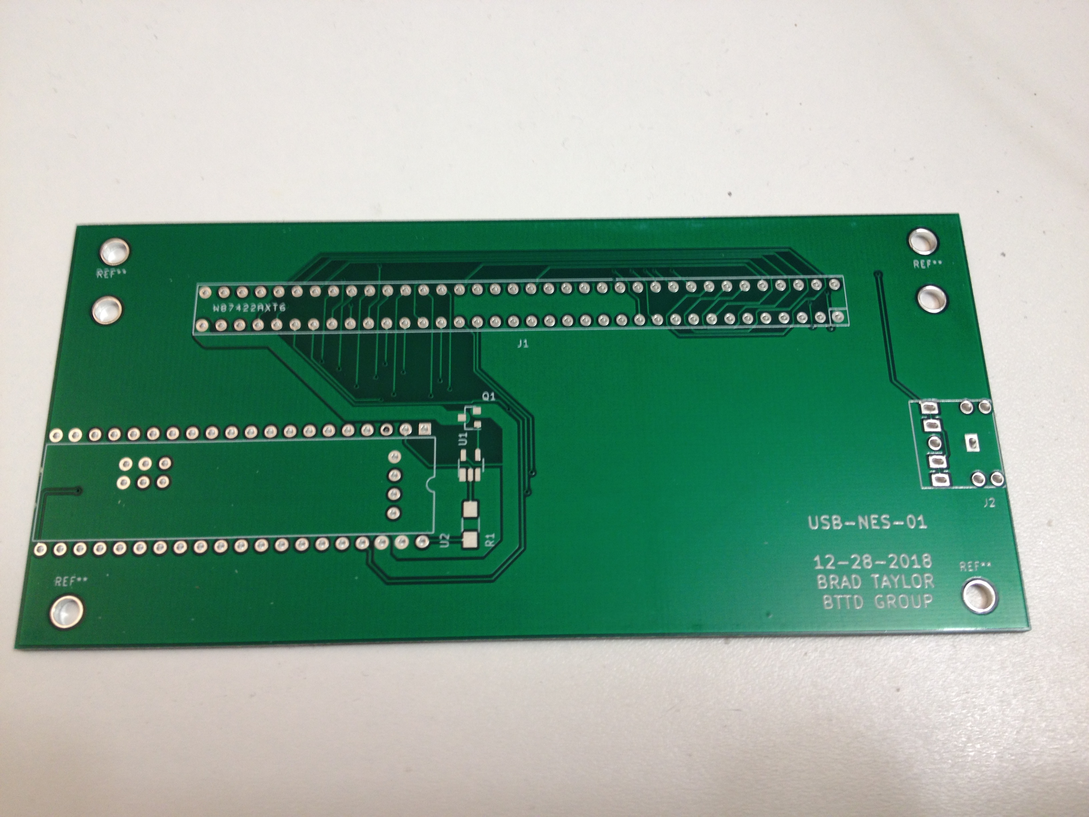
gallery/USB-NES front (unpop).JPG
