digilogistist/The-Open-Source-USB-NES-Project/gallery/USB-NES stuff.JPG

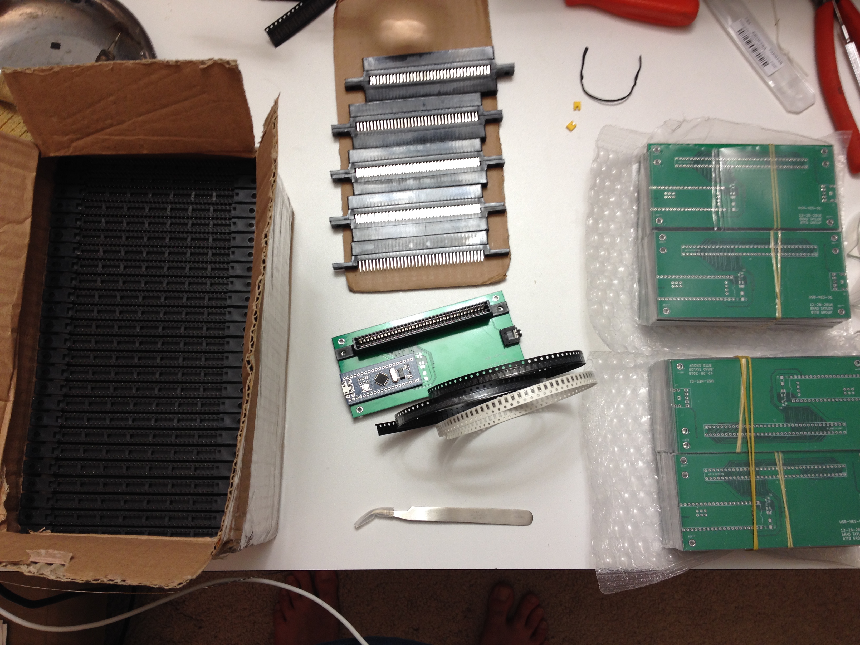
gallery/USB-NES stuff.JPG
