digilogistist/The-Open-Source-USB-NES-Project/gallery/windy white/IMG_1776.JPG

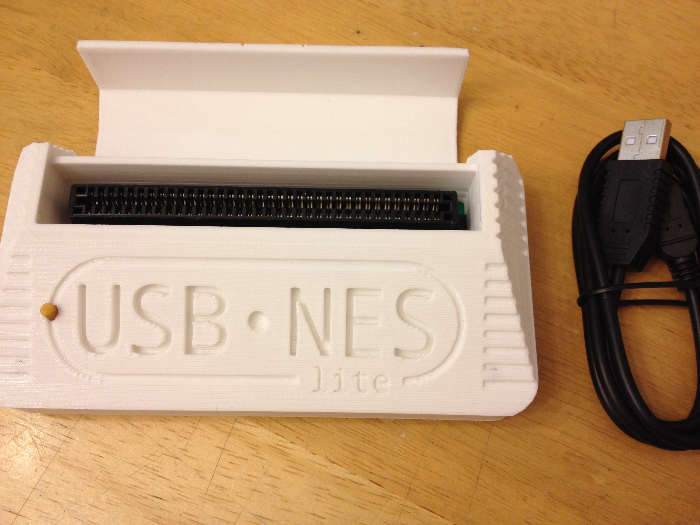
gallery/windy white/IMG_1776.JPG
