digilogistist/The-Open-Source-USB-NES-Project/gallery/windy white/IMG_1778.JPG

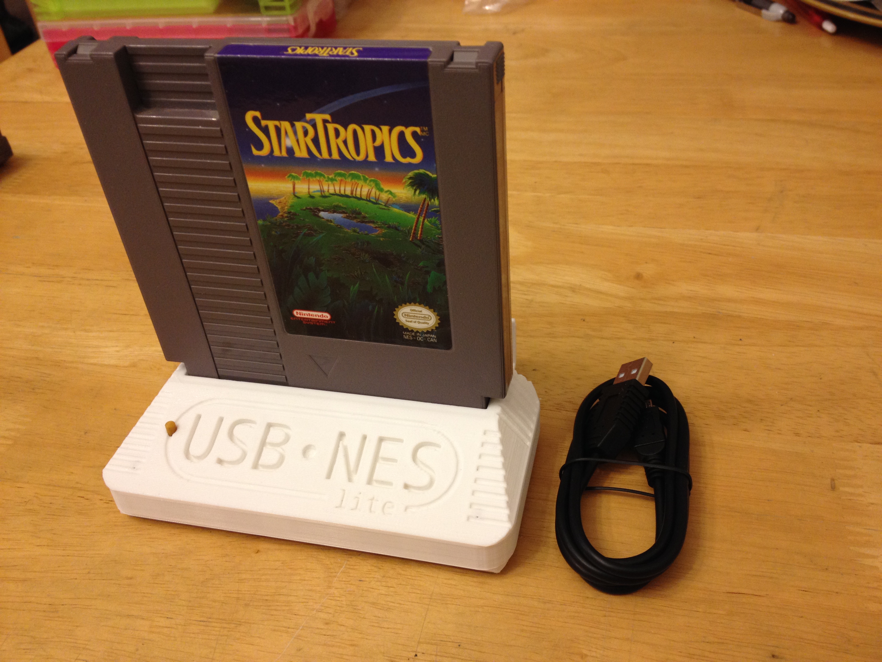
gallery/windy white/IMG_1778.JPG
