digilogistist/The-Open-Source-USB-NES-Project/gallery/windy white/IMG_1779.JPG

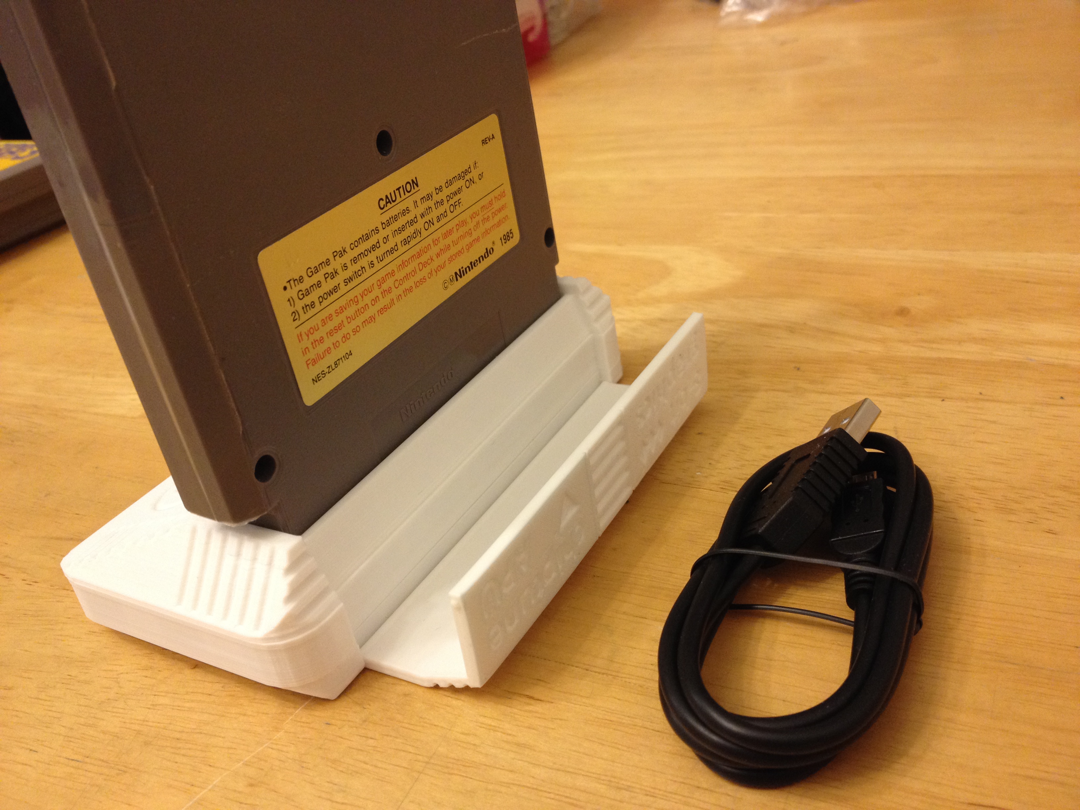
gallery/windy white/IMG_1779.JPG
