digilogistist/The-Open-Source-USB-NES-Project/gallery/windy white/IMG_1853.JPG

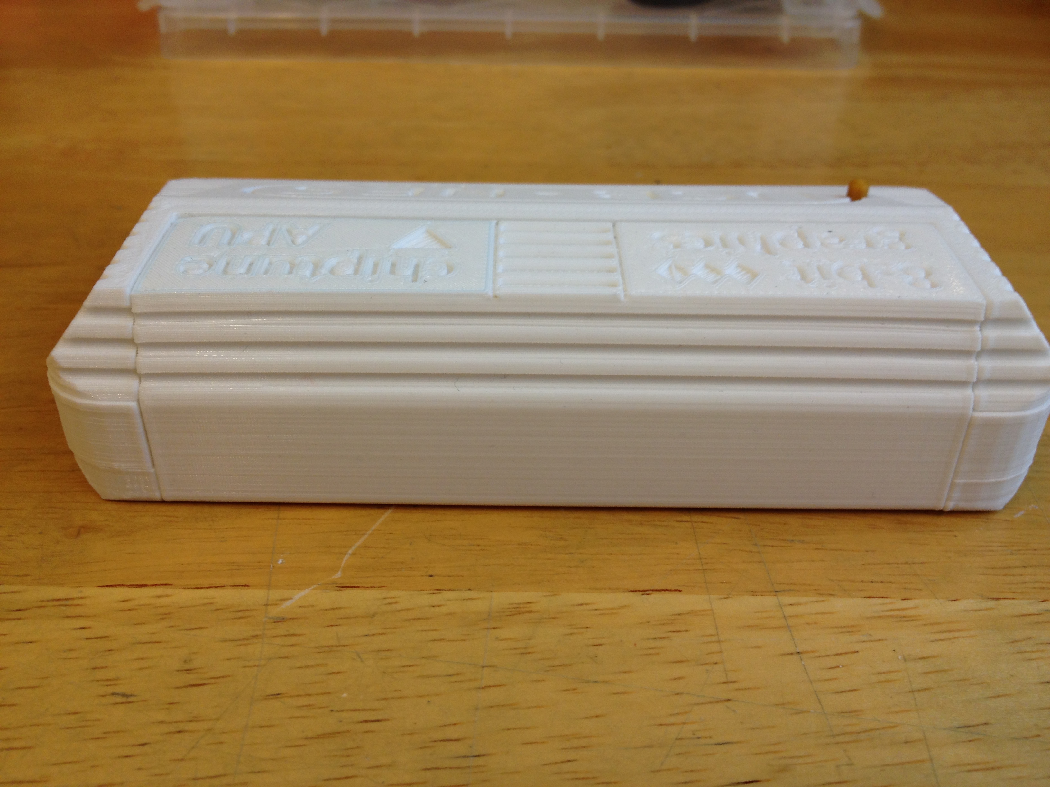
gallery/windy white/IMG_1853.JPG
