digilogistist/The-Open-Source-USB-NES-Project/shell/06-27-2021 USB-NES Lite Dust Cover Hinge.stl

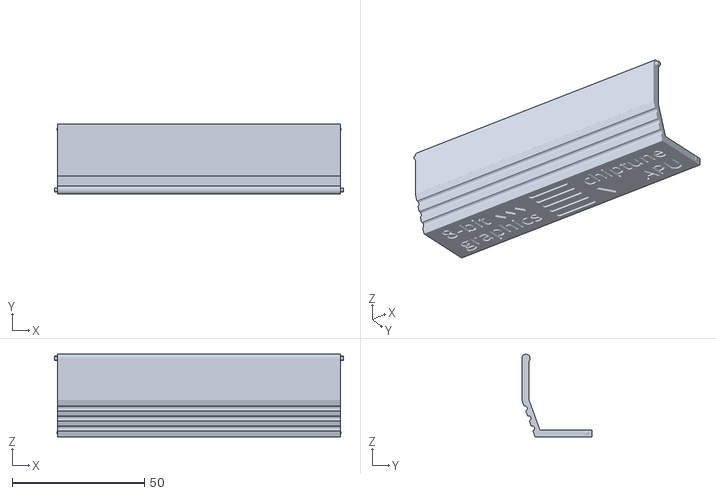
[picture p126: CAD file, 2023-04-14]
shell/06-27-2021 USB-NES Lite Dust Cover Hinge.stl
109.2 x 26.6 x 31.2
