digilogistist/The-Open-Source-USB-NES-Project/shell/(alternate) USB-NES Lite Bottom (no lettering).stl

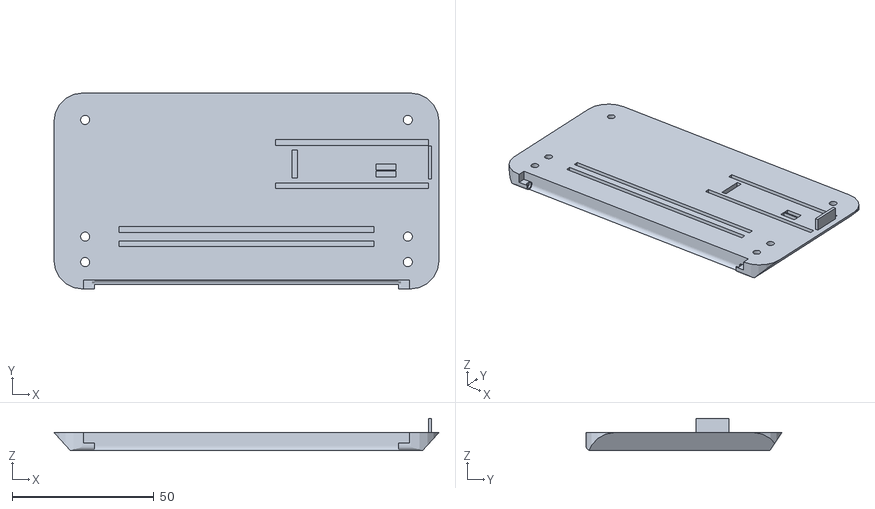
[picture p127: CAD file, 2023-04-14]
shell/(alternate) USB-NES Lite Bottom (no lettering).stl
136.0 x 69.2 x 11.3
