digilogistist/The-Open-Source-USB-NES-Project/shell/03-07-2021 USB-NES Lite Reset Button.stl

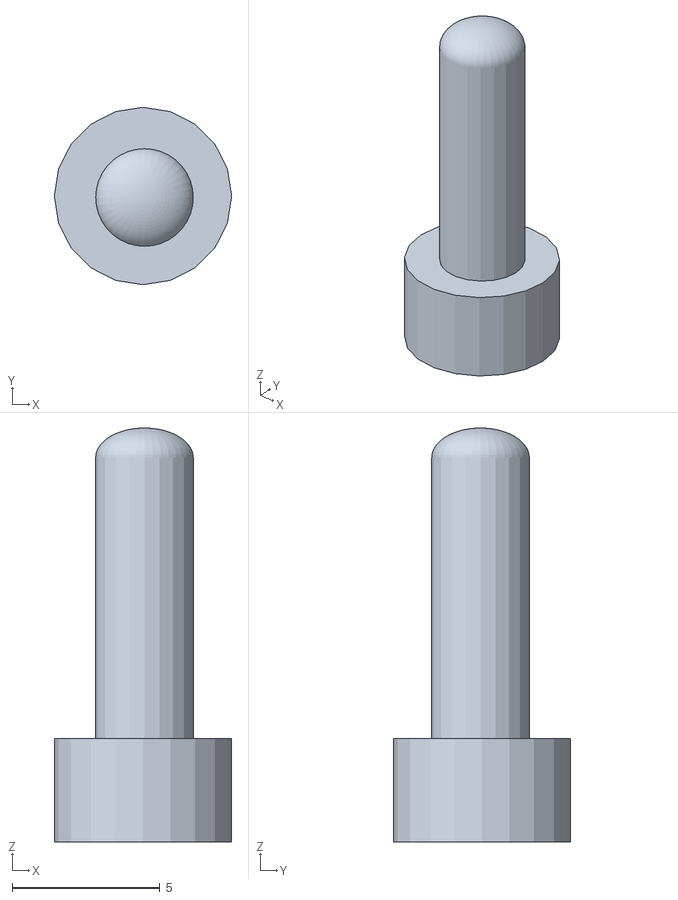
[picture p128: CAD file, 2023-04-14]
shell/03-07-2021 USB-NES Lite Reset Button.stl
6.00 x 6.00 x 14.0
