digilogistist/The-Open-Source-USB-NES-Project/shell/06-24-2021 USB-NES Lite Top.stl

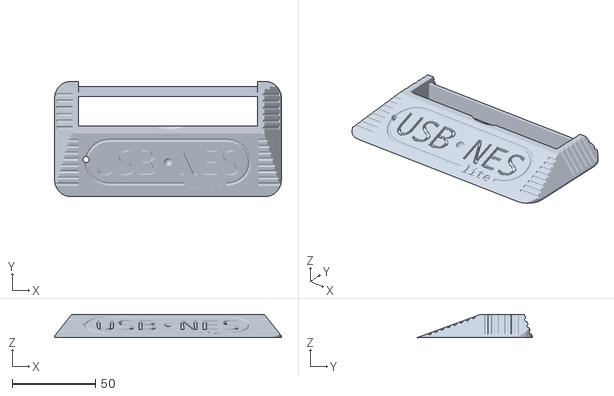
[picture p129: CAD file, 2023-04-14]
shell/06-24-2021 USB-NES Lite Top.stl
136.0 x 69.2 x 13.9
